flyonspeed/OnSpeed-Gen2/Hardware/Photos/IMG_1484.jpg

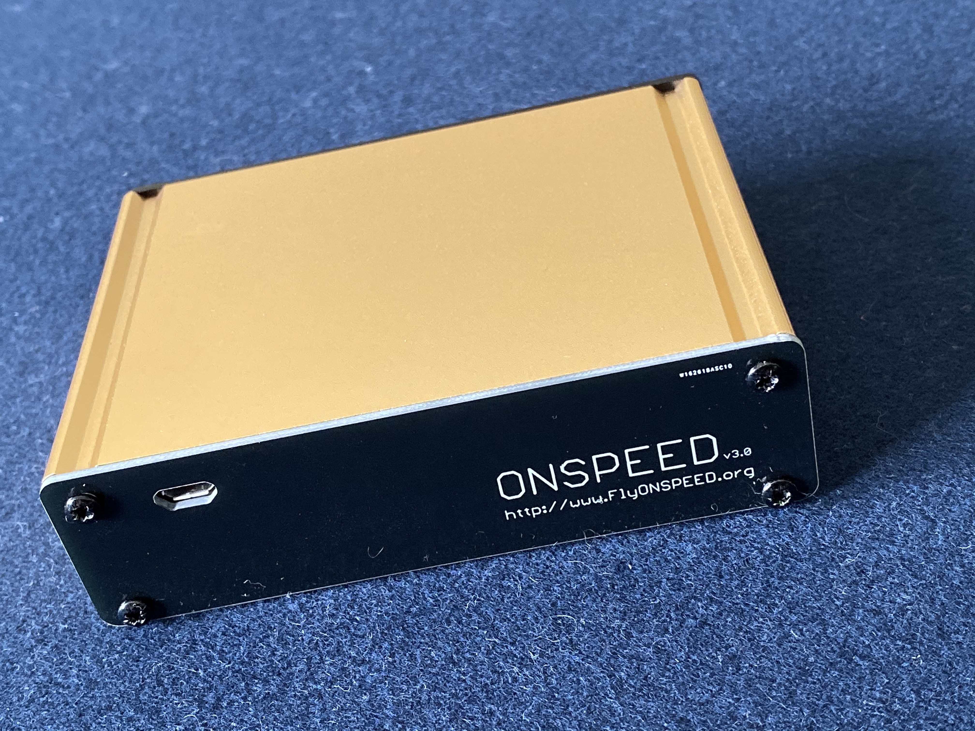
Hardware/Photos/IMG_1484.jpg
