flyonspeed/OnSpeed-Gen2/Hardware/Photos/IMG_8985.JPG

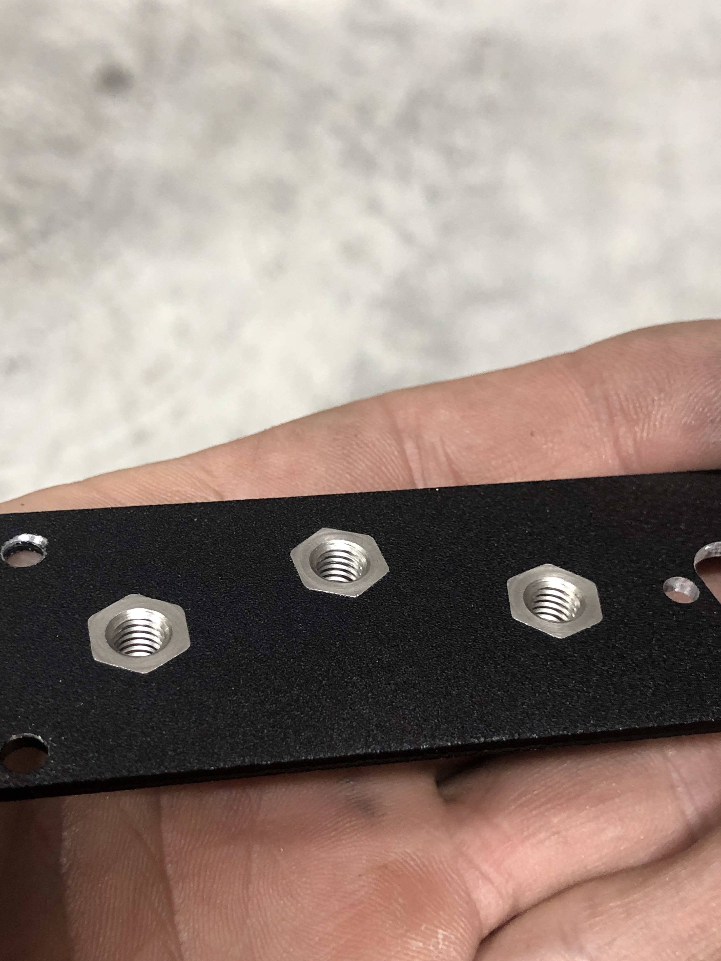
Hardware/Photos/IMG_8985.JPG
