flyonspeed/OnSpeed-Gen2/Hardware/Photos/IMG_8987.JPG

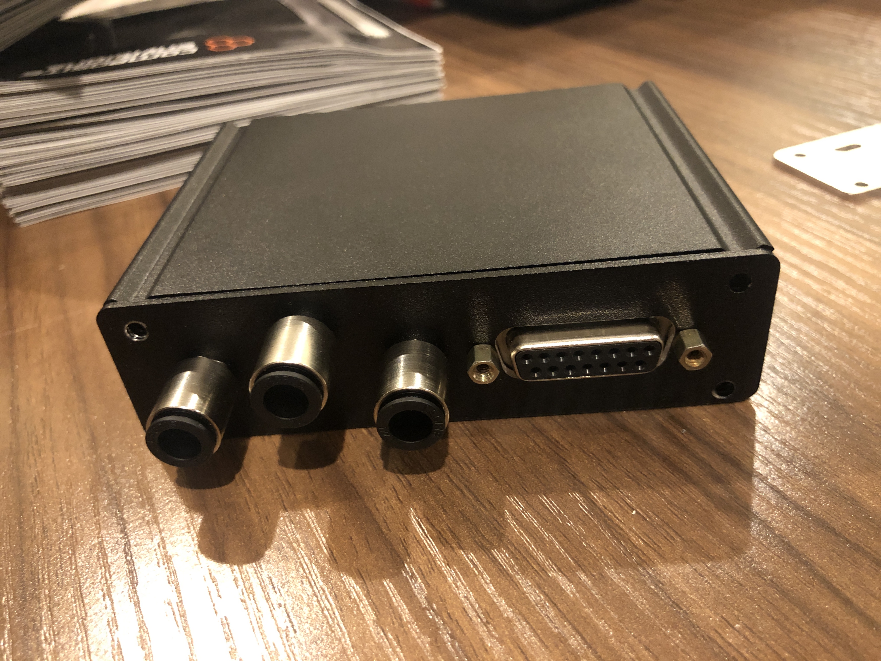
Hardware/Photos/IMG_8987.JPG
