flyonspeed/OnSpeed-Gen2/Hardware/Photos/IMG_9418.jpeg

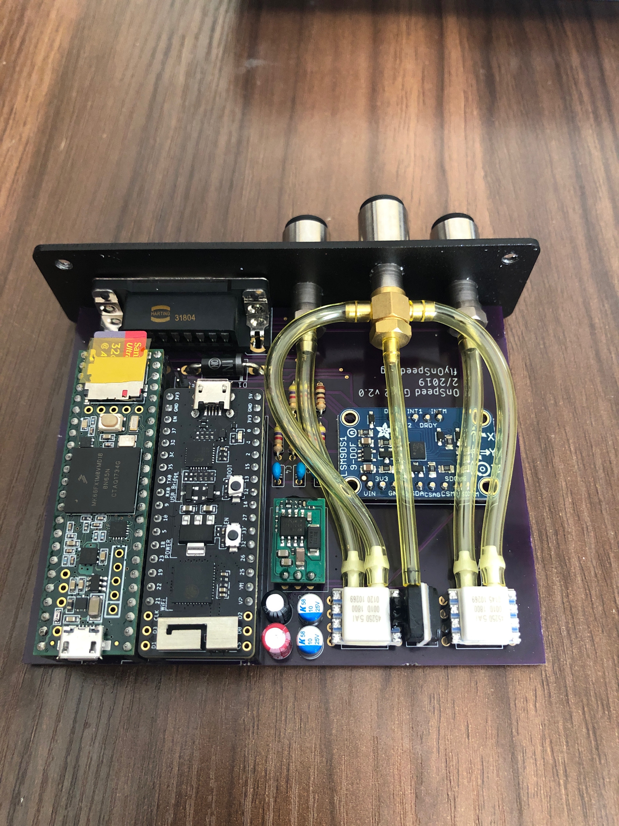
Hardware/Photos/IMG_9418.jpeg
