flyonspeed/OnSpeed-Gen2/Software/OnSpeedTeensy_AHRS/WifiSerial.ino

void readWifiSerial()
{
// read Wifi serial
// look for wifi serial command

if (Serial4.available()>0)
  {
//$LIST!
//$DELETE filename!
//$PRINT filename!
//$STOPLIVEDATA!
//$STARTLIVEDATA!
//$FORMAT!
//$NOLOAD!
//$REBOOT!
//$SENDCONFIGSTRING!
//$SAVECONFIGSTRING<configstring>!
//$VOLUME
//$FLAPS
//$AOA
//$AUDIOTEST
serialWifiCmdChar = Serial4.read();
Serial.print(serialWifiCmdChar);
if (serialWifiCmdBufferSize >=3070)
      {       
      serialWifiCmdBufferSize=0; // don't let the command buffer overflow
      }
  if (serialWifiCmdChar!='!')
    {
    if (serialWifiCmdBufferSize==0 && serialWifiCmdChar!='$')
        {
        //drop character if command doesn't start with $                
        }
         else
              {
              serialWifiCmdBuffer[serialWifiCmdBufferSize]=serialWifiCmdChar;
              serialWifiCmdBufferSize++;
              }
    }          
    if (serialWifiCmdBufferSize>0 && serialWifiCmdChar=='!')
          { 
          // process command          
            if (strstr(serialWifiCmdBuffer, "$LIST"))
              {
              // list files
              timersOff();              
              Serial.println("file list requested on Wifi");
              bool orig_sdLogging=sdLogging;
              if (orig_sdLogging) sdLogging=false; // turn off sdLogging  
              sendWifiSerialString("<filelist>\n");
              ListFile=Sd.open("/", O_READ);
              if (!ListFile) Serial.println("SD card missing or unreadable");
              while(true) {
                          checkWatchdog();
                           FsFile entry =  ListFile.openNextFile();
                           if (!entry) {
                                         // no more files                                                                      
//                                         fileList+="<eof>";
                                         sendWifiSerialString("<eof>\n");
                                         break;
                                        }                           
                           if (!entry.isDirectory())
                              {
                              // only list files in root folder, no directories
                              char entryName[15];
                              entry.getName(entryName, sizeof(entryName));
                              sendWifiSerialString(String(entryName));
                              sendWifiSerialString(":");
                              char entrySize[20];
                              sprintf(entrySize, "%" PRIu64, entry.size());
                              sendWifiSerialString(String(entrySize));
                              sendWifiSerialString("\n");                              
                              }                             
                           entry.close();
                           }                     
               
              if (orig_sdLogging) sdLogging=true; // turn sd logging back on if it was originally on.
              timersOn();
              
              } else
                     if (strstr(serialWifiCmdBuffer, "$DELETE"))
                        {
                        // delete file                        
                        memcpy(listfileFileName,serialWifiCmdBuffer+8,serialWifiCmdBufferSize-7);
                        Sd.remove(listfileFileName);
                        Serial4.println();
                        Serial4.print("Deleted: ");
                        Serial4.println(listfileFileName);
                        } else
                              if (strstr(serialWifiCmdBuffer, "$PRINT"))
                                 {
                                 bool orig_sdLogging=sdLogging;
                                 if (orig_sdLogging)
                                      {
                                      sdLogging=false; // turn off sdLogging                                            
                                      Serial.println("STOPPED SD logging during file transfer.");
                                      }
                                 timersOff();                                                                                                   
                                 // print file contents
                                 Serial.println(serialWifiCmdBuffer);
                                 memcpy(listfileFileName,serialWifiCmdBuffer+7,serialWifiCmdBufferSize-6);                                 
                                 checkWatchdog();
                                 delay(1000);
                                 byte sendBuffer[1460];
                                 int totalBytes=0;
                                 ListFile=Sd.open(listfileFileName, O_READ);
                                 if (ListFile) {     
                                              // read from the file until the end
                                              bool packetFailed=false;
                                              while (ListFile.available())
                                              {      
                                                     checkWatchdog();                                                                                                                                                                                                                                                                                                               
                                                     // wait for serial packet to leave
                                                     if (!packetFailed) totalBytes=ListFile.read(sendBuffer,1459);
                                                     //Serial.println(totalBytes);
                                                     byte checksum=0;                                                     
                                                     for (int i=0;i<totalBytes;i++)
                                                         {                                                     
                                                         while(Serial4.availableForWrite()==0) {};                                                                                                                                                 
                                                         Serial4.write(sendBuffer[i]);                                                                                          
                                                         checksum+=sendBuffer[i];
                                                         }
                                                     Serial4.write(checksum);
                                                     filesendtimer=millis();
                                                     filesendtimeout=false;
                                                     //Serial.println("waiting for checksum");
                                                     while(true)
                                                                      {
                                                                      checkWatchdog();
                                                                      // check for timeout
                                                                      if (millis()-filesendtimer > 5000)
                                                                        {
                                                                         filesendtimeout=true;                                                                         
                                                                         break;  
                                                                        }
                                                                                                                                          
                                                                      // wait for ACK
                                                                      if (Serial4.available())
                                                                        {                                                                                                                                                   
                                                                          byte receivedChecksum=Serial4.read();
                                                                          if (receivedChecksum!=checksum)
                                                                              {
                                                                              packetFailed=true;
                                                                              Serial.print("bad checksum - ");
                                                                              Serial.print(totalBytes);
                                                                              Serial.print(" / ");
                                                                              Serial.print(checksum,HEX);
                                                                              Serial.print(":");
                                                                              Serial.println(receivedChecksum,HEX);
                                                                              Serial.println("resending...");
                                                                              } else
                                                                                    {
                                                                                    packetFailed=false;
                                                                                    }
                                                                         break; // break out of ACK hold                                                                                                                                                                                                                       
                                                                        }                                                                        
                                                                      
                                                                      } // while
                                                         if (filesendtimeout) 
                                                                    {
                                                                      Serial.println("file transfer timeout");
                                                                      break;                                                                                  
                                                                    }                                                               
                                                         // }
                                              }
                                              // close the file:                                              
                                              ListFile.close();                                              
                                              
                                              
                                            } else {
                                              // if the file didn't open, print an error
                                              Serial.print("Could not open file: ");
                                              Serial.println(listfileFileName);
                                              Serial4.print("<404>");
                                              
                                            }                                
                                 if (orig_sdLogging)
                                    {
                                    sdLogging=true; // turn sd logging back on if it was originally on.                                                                        
                                    Serial.println("STARTED SD logging.");
                                    }
                                 timersOn();
                                 } else
                                         
                                         if (strstr(serialWifiCmdBuffer, "$STOPLIVEDATA"))
                                         {
                                         //LiveDisplayTimer.end(); // stop display data 
                                         sendWifiData=false;                                        
                                         Serial.println("STOPPED Live Data. (Wifi Request)");
                                         } else
                                              if (strstr(serialWifiCmdBuffer, "$STARTLIVEDATA"))
                                                 {                                                 
                                                 sendWifiData=true;
                                                 Serial.println("STARTED Live Data. (Wifi Request)");
                                                 } else

                                                   if (strstr(serialWifiCmdBuffer, "$FORMAT"))
                                                          {
                                                          // delete all files                        
                                                          Serial.println("Wifi requested SD format");
                                                           bool orig_sdLogging=sdLogging;
                                                           if (orig_sdLogging) sdLogging=false; // turn off sdLogging 


                                                            ExFatFormatter exFatFormatter;
                                                            FatFormatter fatFormatter;                                                            
                                                            m_card = cardFactory.newCard(SdioConfig(FIFO_SDIO));
                                                            if ((!m_card || m_card->errorCode())) {
                                                                 Serial.print("FORMAT ERROR: Cannot initialize SD card. ");
                                                                 Serial.println(m_card->errorCode());
                                                                 Serial4.println("<formaterror></formaterror>");                                                                 
                                                              } else                                                               
                                                                 {
                                                                  cardSectorCount = m_card->sectorCount();
                                                                  // erase card first
                                                                    Serial.println("Erasing card");
                                                                    uint32_t const ERASE_SIZE = 262144L;
                                                                    uint32_t firstBlock = 0;
                                                                    uint32_t lastBlock;
                                                                    do {
                                                                        lastBlock = firstBlock + ERASE_SIZE - 1;
                                                                        if (lastBlock >= cardSectorCount)
                                                                            {
                                                                            lastBlock = cardSectorCount - 1;
                                                                            }
                                                                        if (!m_card->erase(firstBlock, lastBlock))
                                                                            {
                                                                            Serial.println("Card erase failed");
                                                                            }
                                                                       firstBlock += ERASE_SIZE;
                                                                       checkWatchdog();
                                                                       } while (firstBlock < cardSectorCount);

                                                                  
                                                                    // Format exFAT if larger than 32GB.
                                                                    bool rtn = cardSectorCount > 67108864 ?
                                                                      exFatFormatter.format(m_card, sectorBuffer, &Serial) :
                                                                      fatFormatter.format(m_card, sectorBuffer, &Serial);                                                                  
                                                                    if (!rtn) {
                                                                      Serial.println("FORMAT ERROR: Could not format SD Card.");
                                                                      Serial4.println("<FORMATERROR>Could not format SD Card</FORMATERROR>");
                                                                    } else
                                                                          {
                                                                          Serial.print("SD card format completed. Card size: ");
                                                                          Serial.print(cardSectorCount*5.12e-7);
                                                                          Serial.println("GBytes");
                                                                          Serial4.printf("<FORMATDONE>%.1f GB</FORMATDONE>\n",cardSectorCount*5.12e-7);
                                                                          delay(300);
                                                                          // initialize card, 
                                                                         byte sdBeginTries=0;
                                                                         sdAvailable=Sd.begin(SdioConfig(FIFO_SDIO));
                                                                         while (!sdAvailable && sdBeginTries<5)
                                                                               {
                                                                               //try up to 5 times
                                                                               Serial.println("Reintializing SD card.");
                                                                               sdAvailable=Sd.begin(SdioConfig(FIFO_SDIO));
                                                                               delay(200);
                                                                               sdBeginTries++;
                                                                               }
                                                                          //sdAvailable=Sd.begin(SdioConfig(FIFO_SDIO));
                                                                          if (!sdAvailable) Serial.println("SD card couldn't be initialized");
                                                                          configString="";
                                                                          configurationToString(configString);
                                                                          saveConfigurationToFile(configFilename,configString);
                                                                          configString="";
                                                                          // card is empty create new log file
                                                                          createLogFile();
                                                                                                                                                                                                                           
                                                                          }                                                                    
                                                                 }  
                                                                                                                    
                                                          if (orig_sdLogging)
                                                                {
                                                                sdLogging=true; // turn sd logging back on if it was originally on.
                                                                }
                                                          } else
                                                              if (strstr(serialWifiCmdBuffer, "$PFWDBIAS"))
                                                                  {                                                                  
                                                                  SensorTimer.end(); // stop polling the sensors on the timer so we can poll them here
                                                                  Serial.println("Wifi: Getting Pfwd bias...");
                                                                  // get Pfwd bias
                                                                  long PfwdTotal=0;                                                                
                                                                  for (int i=1;i<=500;i++)
                                                                      {
                                                                      PfwdTotal+=GetPressurePfwd();
                                                                      checkWatchdog();
                                                                      delay(2);
                                                                      }
                                                                 Serial4.printf("<PFWDBIAS>%i</PFWDBIAS>",round(PfwdTotal/500));
                                                                 SensorTimer.begin(SensorRead,SENSOR_INTERVAL);                                                                                                                               
                                                                  } else
                                                                      if (strstr(serialWifiCmdBuffer, "$P45BIAS"))
                                                                      {                                                                  
                                                                      SensorTimer.end(); // stop polling the sensors on the timer so we can poll them here
                                                                      Serial.println("Wifi: Getting P45 bias...");
                                                                      // get Pfwd bias                                                                      
                                                                      long P45Total=0;
                                                                      for (int i=1;i<=500;i++)
                                                                          {                                                                          
                                                                          P45Total+=GetPressureP45();
                                                                          delay(2);
                                                                          checkWatchdog();
                                                                          }
                                                                      Serial4.printf("<P45BIAS>%i</P45BIAS>",round(P45Total/500));
                                                                      SensorTimer.begin(SensorRead,SENSOR_INTERVAL);                                                                                                                               
                                                                      } else
                                                                            if (strstr(serialWifiCmdBuffer, "$FLAPS"))
                                                                                {                                                                                                                                              
                                                                                Serial.println("Wifi: Getting Flap position");
                                                                                int flapPotTotal=0;
                                                                                for (int i=0;i<100;i++)
                                                                                    {
                                                                                    flapPotTotal+=analogRead(FLAP_PIN);
                                                                                    checkWatchdog();
                                                                                    delay(10);
                                                                                    }                                                                                                      
                                                                                Serial4.printf("<FLAPS>%i</FLAPS>",round(flapPotTotal/100));                                                                                                                                
                                                                                } else
                                                                                  if (strstr(serialWifiCmdBuffer, "$VOLUME"))
                                                                                        {                                                                                                                                              
                                                                                        Serial.println("Wifi: Getting Volume position");
                                                                                        int volumePotTotal=0;
                                                                                        for (int i=0;i<100;i++)
                                                                                            {
                                                                                            volumePotTotal+=analogRead(VOLUME_PIN);
                                                                                            checkWatchdog();
                                                                                            delay(10);
                                                                                            }                                                                                                              
                                                                                        Serial4.printf("<VOLUME>%i</VOLUME>",round(volumePotTotal/100));                                                                                                                                
                                                                                        } else                                                                                                          
                                                                                              if (strstr(serialWifiCmdBuffer, "$AUDIOTEST"))                                                                                                                                                                          
                                                                                                {
                                                                                                Serial.println("Wifi: Testing audio");
                                                                                                timersOff();
                                                                                                Serial.println("Wifi: Playing Left audio test");                                                                                                                  
                                                                                                 ampLeft.gain(1);
                                                                                                 ampRight.gain(0);
                                                                                                 voice1.play(AudioSampleOnspeed_left_speaker);
                                                                                                checkWatchdog();
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
                                                                                                                                          for (unsigned int i=0;i<configContent.length();i++) calcCRC+=configContent[i];
                                                                                                                                          if (String(calcCRC,HEX)==checksumString)
                                                                                                                                              {
                                                                                                                                              // checksum ok.
                                                                                                                                              configString="<CONFIG>"+configContent+"</CONFIG>"; // strip checksum tag when saving config
                                                                                                                                              if (loadConfigFromString(configString))
                                                                                                                                                  {                                                                                                                                                
                                                                                                                                                  saveConfigurationToFile(configFilename,configString);
                                                                                                                                                  setVolume(volumePercent);
                                                                                                                                                  configureAxes();
                                                                                                                                                  Serial4.print("<CONFIGSAVED></CONFIGSAVED>"); 
                                                                                                                                                  Serial.println("Wifi: Loaded new configuration");                                                                                                                
                                                                                                                                                  } else Serial4.print("<CONFIGERROR>Could not load configuration</CONFIGERROR>");                                                                                                                                              
                                                                                                                                          
                                                                                                                                                } else
                                                                                                                                                      {
                                                                                                                                                      //checksum failed
                                                                                                                                                      Serial4.print("<CONFIGERROR>Transmission Error. Checksum failed. Try again.</CONFIGERROR>");
                                                                                                                                                      Serial.println("CONFIG checksum failed");
                                                                                                                                                      }
                                                                                                                                           checkWatchdog();
                                                                                                                                          // clean up after the strings 
                                                                                                                                          configString="";
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
                                                                                                                                                            timersOn(); 
                                                                                                                                                            sdLogging=true;    
                                                                                                                                                            } else
                                                                                                                                                                if (strstr(serialWifiCmdBuffer, "$SENSORCONFIG"))
                                                                                                                                                                    {
                                                                                                                                                                    // sensor bias configuration
                                                                                                                                                                     float aircraftPitch=stringToFloat(getConfigValue(serialWifiCmdBuffer,"AIRCRAFTPITCH"));
                                                                                                                                                                     float aircraftRoll=stringToFloat(getConfigValue(serialWifiCmdBuffer,"AIRCRAFTROLL"));
                                                                                                                                                                     float aircraftPAlt=stringToFloat(getConfigValue(serialWifiCmdBuffer,"AIRCRAFTPALT"));
                                                                                                                                                                     sdLogging=false;
                                                                                                                                                                     timersOff();

                                                                                                                                                                     Serial.println("Wifi: SensorConfig request");
                                                                                                                                                                     // sample sensors
                                                                                                                                                                     long P45Total=0;
                                                                                                                                                                     long PFwdTotal=0;
                                                                                                                                                                     long PStaticTotal=0;
                                                                                                                                                                     float aVertTotal=0.00;
                                                                                                                                                                     float aLatTotal=0.00;
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
                                                                                                                                                                          }
                                                                                                                                                                       
                                                                                                                                                                     // calculate pitch from averaged accelerometer reading
                                                                                                                                                                     float calcPitch=atan2((aFwdTotal/sensorReadCount), sqrt((aLatTotal/sensorReadCount)* (aLatTotal/sensorReadCount) + (aVertTotal/sensorReadCount) *(aVertTotal/sensorReadCount))) * 57.2957;
                                                                                                                                                                     float calcRoll =-atan2((aLatTotal/sensorReadCount), sqrt((aFwdTotal/sensorReadCount)* (aFwdTotal/sensorReadCount) + (aVertTotal/sensorReadCount) *(aVertTotal/sensorReadCount))) * 57.2957;                                                                                                                                                                     
                                                                                                                                                                     // adjust pitch bias (aircraft pitch -calcPitch)
                                                                                                                                                                     pitchBias=aircraftPitch-calcPitch;
                                                                                                                                                                     rollBias=aircraftRoll-calcRoll;
                                                                                                                                                                     Serial.printf("aircraftPitch: %.2f,aircraftRoll: %.2f,calcPitch: %.2f,calcRoll: %.2f",aircraftPitch,aircraftRoll,calcPitch,calcRoll);
                                                                                                                                                                     pFwdBias= int((PFwdTotal/sensorReadCount));
                                                                                                                                                                     p45Bias= int((P45Total/sensorReadCount));
                                                                                                                                                                     float PStatic= float((PStaticTotal/sensorReadCount));
                                                                                                                                                                     float aircraftPressure=29.92125535*pow(((288-0.0065*0.3048*aircraftPAlt)/288),5.2561)*33.8639; // https://www.weather.gov/media/epz/wxcalc/stationPressure.pdf from inHg to milliBars.
                                                                                                                                                                     pStaticBias=aircraftPressure - PStatic;

                                                                                                                                                                     
                                                                                                                                                                     gxBias=-gxTotal/sensorReadCount;
                                                                                                                                                                     gyBias=-gyTotal/sensorReadCount;
                                                                                                                                                                     gzBias=-gzTotal/sensorReadCount;
                                                                                                                                                                     
 
                                                                                                                                                                     String resultString="PfwdBias: "+ String(pFwdBias)+"<br>";
                                                                                                                                                                     resultString+=" P45Bias: "+ String(p45Bias)+"<br>";
                                                                                                                                                                     resultString+=" gxBias: "+ floatToString(gxBias)+"<br>";
                                                                                                                                                                     resultString+=" gyBias: "+ floatToString(gyBias)+"<br>";
                                                                                                                                                                     resultString+=" gzBias: "+ floatToString(gzBias)+"<br>";
                                                                                                                                                                     resultString+=" measured Pitch: "+ String(calcPitch)+"<br>"; 
                                                                                                                                                                     resultString+=" pitchBias: "+ String(pitchBias)+"<br>";
                                                                                                                                                                     resultString+=" measured Roll: "+ String(calcRoll)+"<br>"; 
                                                                                                                                                                     resultString+=" rollBias: "+ String(rollBias)+"<br>"; 
                                                                                                                                                                     resultString+=" staticBias: "+ String(pStaticBias)+"<br>";                                                                                                                                                                     
                                                                                                                                                                     configString="";
                                                                                                                                                                     configurationToString(configString);
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
                                                                                                                                                                                            }
                                                                                                                                                                                             
                                                                                                                                                                                        // calculate pitch from averaged accelerometer reading                                                                                                                                                                                       
                                                                                                                                                                                        float calcPitchAngle=calcPitch(aFwdTotal/sensorReadCount, aLatTotal/sensorReadCount, aVertTotal/sensorReadCount);
                                                                                                                                                                                        float calcRollAngle=calcRoll(aFwdTotal/sensorReadCount, aLatTotal/sensorReadCount, aVertTotal/sensorReadCount);
                                                                                                                                                                                        float PStatic= float((PStaticTotal/sensorReadCount));
                                                                                                                                                                                        Palt=145366.45*(1-pow((PStatic+pStaticBias)/1013.25,0.190284)); //Pstatic in milliBars,Palt in feet
                                                                                                                                                                                        Serial4.printf("<RESPONSE><PITCH>%.2f</PITCH><ROLL>%.2f</ROLL><PALT>%.2f</PALT></RESPONSE>",calcPitchAngle,-calcRollAngle,Palt);                                                                                                                                                                                     
                                                                                                                                                                                        timersOn();
                                                                                                                                                                                        sdLogging=true;
                                                                                                                                                                                        }  else
                                                                                                                                                                                              if (strstr(serialWifiCmdBuffer, "$VERSION"))
                                                                                                                                                                                                        {
                                                                                                                                                                                                         Serial.println("Wifi: Version request");
                                                                                                                                                                                                         sendWifiSerialString("<VERSION>"+String(VERSION)+"</VERSION>");                                                                                                                                                                                                    
                                                                                                                                                                                                        }
                                                                                                                                                                                                         else                                                                                                                                                                                                                                                                                                        
                                                                                                                                                                                                             if (strstr(serialWifiCmdBuffer, "$VNOCHIMETEST"))                                                                                                                                                                          
                                                                                                                                                                                                                    {
                                                                                                                                                                                                                    Serial.println("Wifi: VNO chime audiotest");
                                                                                                                                                                                                                    timersOff();                                                                                                                                                                                                         
                                                                                                                                                                                                                    voice1.play(AudioSampleVnochime);
                                                                                                                                                                                                                    checkWatchdog();
                                                                                                                                                                                                                    delay (2500);
                                                                                                                                                                                                                    checkWatchdog();                                                                                                                                                                                                       
                                                                                                                                                                                                                    timersOn();
                                                                                                                                                                                                                    Serial.println("Wifi: VNOCHIMETEST Complete");
                                                                                                                                                                                                                    Serial4.println("<VNOCHIMETEST>Done.</VNOCHIMETEST>");
                                                                                                                                                                                                                    }

          // reset cmdBuffer
          memset(serialWifiCmdBuffer,0,sizeof(serialWifiCmdBuffer));
          serialWifiCmdBufferSize=0;
          }  
  } // if serial.available wifi

}

void sendWifiSerialString(String serialString)
{
  for (unsigned int i=0; i<serialString.length();i++)
  {
  Serial4.flush();
  while(Serial4.availableForWrite() == 0)
    {
    checkWatchdog();
    };
  Serial4.print(serialString[i]);  
  checkWatchdog();
  }
}
