flyonspeed/OnSpeed-Gen2/Software/OnSpeedWifi/html_liveview.h

const char htmlLiveView[] PROGMEM = R"=====(
<style>

html, body { margin:0; padding: 0 5px; overflow:hidden;min-height:100% }

#container {width:100%}  

svg {position:absolute;margin:0 auto; display: block;}

#datafields {position:relative; margin-top:5px;font-family: "Arial, Helvetica, sans-serif";font-size:16px; left:0px;}

#footer {display: block;;position:fixed; bottom:2px; width: 100%;font-family: "Arial, Helvetica, sans-serif";font-size:14px;}

#footer-warning {text-align: center;margin-left: -10px; width: 100%;font-family: "Arial, Helvetica, sans-serif";font-size:12px;background-color:white}

#status {display:flex;justify-content: space-between;padding-bottom:10px;}

#switch {margin-right: 20px;}  

#status-label {align-self: flex-end;}  

/*! XS */

@media (orientation: portrait) {

  svg {  margin: 0 auto 0 0px; }

}

@media (orientation: landscape) {

 /* svg { height: 60vh;}*/  

}

</style>

<script language="javascript" type="text/javascript">
 var wsUri = "ws://192.168.0.1:81";
 var lastUpdate= Date.now();
 var lastDisplay=Date.now(); 
 var AOA=0;
 var IAS=0;
 var PAlt=0;
 var GLoad=1;
 var GLoadLat=0;
 var PitchAngle=0;
 var RollAngle=0;
 var smoothingAlpha=.9;
 var liveConnecting=false;
 var flightPath=0;
 var iVSI=0;
 var derivedAOA=0;
 var pitchRate=0;

 var calSource="";
setInterval(updateAge,500); 
var websocket;


function init()

  {            
     writeToStatus("CONNECTING...");
     liveConnecting=true;
     setTimeout(connectWebSocket, 300);   
    
  }



function connectWebSocket()

  { 

    websocket = new WebSocket(wsUri);

    websocket.onopen = function(evt) { onOpen(evt) };

    websocket.onclose = function(evt) { onClose(evt) };

    websocket.onmessage = function(evt) { onMessage(evt) };

    websocket.onerror = function(evt) { onError(evt) };

  }



  function onOpen(evt)

  {
    writeToStatus("CONNECTED");
  }



  function onClose(evt)
  {
    writeToStatus("Reconnecting...");    
    if (!liveConnecting) setTimeout(connectWebSocket, 10);
  }

  

 function map(x, in_min, in_max, out_min, out_max)

{

if ((in_max - in_min) + out_min ==0) return 0;

  return (x - in_min) * (out_max - out_min) / (in_max - in_min) + out_min;

}  



  function onMessage(evt)

  {    
   // reply to prevent timeouts
   liveConnecting=false;
   // connected, got data
   // smoother values are display with the formula: value = measurement*alpha + previous value*(1-alpha)   

   try {

   //console.log(evt.data);

   OnSpeedArray = evt.data.split(",");

   var OnSpeed = new Object();

   OnSpeed.AOA= OnSpeedArray[1]; 

   OnSpeed.Pitch= OnSpeedArray[2]; 

   OnSpeed.Roll= OnSpeedArray[3]; 

   OnSpeed.IAS= OnSpeedArray[4]; 

   OnSpeed.PAlt= OnSpeedArray[5]; 

   OnSpeed.verticalGLoad= OnSpeedArray[6]; 

   OnSpeed.lateralGLoad= OnSpeedArray[7]; 

   OnSpeed.alphaVA= OnSpeedArray[8]; 

   OnSpeed.LDmax= OnSpeedArray[9]; 

   OnSpeed.OnspeedFast= OnSpeedArray[10]; 

   OnSpeed.OnspeedSlow= OnSpeedArray[11]; 

   OnSpeed.OnspeedWarn= OnSpeedArray[12]; 

   OnSpeed.flapsPos= OnSpeedArray[13]; 

   OnSpeed.coeffP= OnSpeedArray[14];

   OnSpeed.dataMark= OnSpeedArray[15];

   OnSpeed.kalmanVSI=OnSpeedArray[16];
   
   OnSpeed.flightPath=OnSpeedArray[17]

   OnSpeed.PitchRate= OnSpeedArray[18];
   
   OnSpeed.DecelRate= OnSpeedArray[19];

   OnSpeed.calSourceID= OnSpeedArray[20];
      
   OnSpeed.CRC= OnSpeedArray[21]; 

   var crc_string=OnSpeed.AOA+','+OnSpeed.Pitch+','+OnSpeed.Roll+','+OnSpeed.IAS+','+OnSpeed.PAlt+','+OnSpeed.verticalGLoad+','+OnSpeed.lateralGLoad+','+OnSpeed.alphaVA+','+OnSpeed.LDmax+','+OnSpeed.OnspeedFast+','+OnSpeed.OnspeedSlow+','+OnSpeed.OnspeedWarn+','+OnSpeed.flapsPos+','+OnSpeed.coeffP+','+OnSpeed.dataMark+','+OnSpeed.kalmanVSI+','+OnSpeed.flightPath+','+OnSpeed.PitchRate+','+OnSpeed.DecelRate+','+OnSpeed.calSourceID;
   //console.log("CRC",crc_string);

   var crc_calc=0;

   for (i=0;i<crc_string.length;i++)

       {

       crc_calc+=crc_string.charCodeAt(i);

     crc_calc=crc_calc & 0xFF;

     }

    if (OnSpeed.CRC==crc_calc)

    {

    // CRC ok, use values

    AOA=(OnSpeed.AOA*smoothingAlpha+AOA*(1-smoothingAlpha)).toFixed(2);

    IAS=(OnSpeed.IAS*smoothingAlpha+IAS*(1-smoothingAlpha)).toFixed(2);

    PAlt=(OnSpeed.PAlt*smoothingAlpha+PAlt*(1-smoothingAlpha)).toFixed(2);

    GLoad=(OnSpeed.verticalGLoad*smoothingAlpha+GLoad*(1-smoothingAlpha)).toFixed(2);

    GLoadLat=(OnSpeed.lateralGLoad*smoothingAlpha+GLoadLat*(1-smoothingAlpha)).toFixed(2);

    PitchAngle=(OnSpeed.Pitch*smoothingAlpha+PitchAngle*(1-smoothingAlpha)).toFixed(2);

    RollAngle=(OnSpeed.Roll*smoothingAlpha+RollAngle*(1-smoothingAlpha)).toFixed(2);

    iVSI=(OnSpeed.kalmanVSI*smoothingAlpha+iVSI*(1-smoothingAlpha)).toFixed(2);

    flightPath=(OnSpeed.flightPath*smoothingAlpha+flightPath*(1-smoothingAlpha)).toFixed(2);

    derivedAOA=(PitchAngle-flightPath).toFixed(2);

    pitchRate=parseFloat(OnSpeed.PitchRate);

    LDmax=parseFloat(OnSpeed.LDmax);

    OnspeedFast=parseFloat(OnSpeed.OnspeedFast);

    OnspeedSlow=parseFloat(OnSpeed.OnspeedSlow);

    OnspeedWarn=parseFloat(OnSpeed.OnspeedWarn);
    lastUpdate=Date.now();
    // 0= IMU, 1=VN-300, 2=AFS/SkyView, 3=Dynon D10, 4=G5, 5=G3X, 6=MGL
      switch (parseInt(OnSpeed.calSourceID)) {
      case 0:
      calSource="Internal IMU";
      break;
      case 1: calSource="VectorNav VN-200/300";
        break;
      case 2: calSource="SkyView/Advanced";
        break;
      case 3: calSource="Dynon D10/D100";
        break;
      case 4: calSource="Garmin G5";
        break;
      case 5: calSource="Garmin G3X";
        break;
      case 6: calSource="MGL iEFIS";
        break;      
      default:
        calSource='N/A';
  }
    
      writeToCalibrationSource(calSource); 

    //console.log('log:',AOA,IAS,PAlt,GLoad,GLoadLat,PitchAngle,OnSpeed.LDmax,OnSpeed.OnspeedFast,OnSpeed.OnspeedSlow,OnSpeed.OnspeedWarn);

    // move AOA line on display    

   if (AOA<=LDmax)
  
     {

     var aoaline_y=map(AOA, 0, LDmax, 278, 228);     

     } else

     if (AOA>LDmax && AOA<=OnspeedFast)

       {

       aoaline_y=map(AOA, LDmax, OnspeedFast, 228, 178);

       } else

       if (AOA>OnspeedFast && AOA<=OnspeedSlow)

         {

         aoaline_y=map(AOA, OnspeedFast, OnspeedSlow, 178, 113);

         } else

             if (AOA>OnspeedSlow)

               {

               aoaline_y=map(AOA, OnspeedSlow,OnspeedWarn, 113, 15);

               //console.log('aoaline',aoaline_y,AOA,OnspeedSlow,OnspeedWarn);

               }



    document.getElementById("aoaline").setAttribute("y", aoaline_y);

// calc ldmax dot locations

 ldmax_y=228+3;

 document.getElementById("ldmaxleft").setAttribute("cy", ldmax_y);

 document.getElementById("ldmaxright").setAttribute("cy", ldmax_y);

// show onspeed dot

// update attitude

updateAttitude(OnSpeed.Pitch,OnSpeed.Roll);

 if (AOA>OnspeedFast && AOA<=OnspeedSlow) document.getElementById("onspeeddot").style.visibility="visible"; else document.getElementById("onspeeddot").style.visibility="hidden"; 

   

}  else console.log('CRC error'); 

    

   } catch (e) {

           console.log('JSON parsing error:'+e.name+': '+e.message);

           }         

   

   if (Date.now()-lastDisplay>=500)

       {

       if (AOA > -20) document.getElementById("aoa").innerHTML=AOA; else document.getElementById("aoa").innerHTML='N/A';

       document.getElementById("ias").innerHTML=IAS +' kts';

       document.getElementById("palt").innerHTML=PAlt+' ft';

       document.getElementById("ivsi").innerHTML=iVSI+' fpm';

       document.getElementById("gload").innerHTML=GLoad+' G';

       document.getElementById("gloadLat").innerHTML=GLoadLat+' G';

       document.getElementById("pitch").innerHTML=PitchAngle+'&#176;';

       document.getElementById("roll").innerHTML=RollAngle+'&#176;';

       document.getElementById("flightpath").innerHTML=flightPath+'&#176;';

       document.getElementById("derivedaoa").innerHTML=derivedAOA+'&#176;';

       document.getElementById("datamark").innerHTML=OnSpeed.dataMark;

       document.getElementById("flapspos").innerHTML=OnSpeed.flapsPos+'&#176;';

       lastDisplay=Date.now(); 

   }

  

  }



 function onError(evt)

  {
    console.log(evt.data);
    
    writeToStatus(evt.data);

  }  



  function updateAge()

  {

  var age=((Date.now()-lastUpdate)/1000).toFixed(1);   

  if (document.getElementById("age"))

    {

   document.getElementById("age").innerHTML=age +' sec';

   if (age>=1)  document.getElementById("age").style="color:red"; else document.getElementById("age").style="color:black";         

   if ((age>=3) && !liveConnecting) init();    

   }

  }



 function writeToStatus(message)

  {

    var status = document.getElementById("connectionstatus");

    status.innerHTML = message;

  } 

 function writeToCalibrationSource(calSource)
  {

    var status = document.getElementById("calibrationsource");

    status.innerHTML = calSource;

  }   

 function updateAttitude(pitch,roll) {

  if (document.getElementById("attitude")==null || document.getElementById("attitude").style.visibility!="visible") return; //don't update attitude if attitude indicator is not visible

    roll=roll*-1;

    var p = (pitch * 2.50);

    var t = 'translate(50,50) rotate(' + roll + ') translate(0,' + p + ')' ;

    var id_roll = document.querySelector('#onspeed-attitude-pos');

    if (id_roll!=null) id_roll.setAttribute('transform',t);

  var id_dial = document.querySelector('#onspeed-attitude-dial');

  x = 50;

    y = 50;

    var t =  'translate(' + x + ',' + y + ')' + 'rotate(' + roll + ')';

    id_dial.setAttribute('transform',t);   

  }



function toggleAOA(state)

  {

  //console.log(state);

  if (state)

      {

      document.getElementById("aoaindexer").style.visibility="visible";

      document.getElementById("attitude").style.visibility="hidden";   

      } else

            {

            document.getElementById("aoaindexer").style.visibility="hidden";

            document.getElementById("attitude").style.visibility="visible";   

            }

}            

updateAttitude(0,0);

//window.addEventListener("load", function() {init();}, false);  

</script>

<div id="container">

  <div id="aoaindexer">

  <svg version="1.1" viewBox="0 0 210 297" width="100%" style="height: 70vh">

 <g>

  <circle cx="98.171" cy="787.76" r="133.84" fill="#07a33f" stroke-width="1.8089"/>

  <rect transform="rotate(-15.029)" x="50.364" y="33.747" width="15.615" height="89.228" fill="#cc3837"/>

  <rect transform="matrix(-.9658 -.2593 -.2593 .9658 0 0)" x="-148.06" y="-19.129" width="15.615" height="89.228" fill="#cc3837"/>

  <rect transform="matrix(.9658 .2593 .2593 -.9658 0 0)" x="127.53" y="-255.15" width="15.615" height="89.228" fill="#f49421"/>

  <rect transform="rotate(164.97)" x="-70.153" y="-307.83" width="15.615" height="89.228" fill="#f49421"/>

  <path d="m101.8 113.26c-17.123 0-31.526 12.231-34.92 28.385 5.203-2.6e-4 10.398 1.6e-4 15.598 0 2.9178-7.8426 10.401-13.371 19.323-13.371 8.922 0 16.413 5.5289 19.336 13.371 5.198 1.6e-4 10.403-2.8e-4 15.602 0-3.397-16.154-17.815-28.385-34.938-28.385zm-35.121 41.774c2.9176 16.746 17.577 29.609 35.121 29.609 17.544 0 32.218-12.863 35.138-29.609-5.1216-2.8e-4 -10.25 1.6e-4 -15.371 0-2.5708 8.4824-10.391 14.574-19.767 14.574-9.3764 0-17.183-6.0913-19.75-14.574-5.1246 1.4e-4 -10.244-2.8e-4 -15.371 0z" color="#000000" color-rendering="auto" dominant-baseline="auto" fill="#07a33f" image-rendering="auto" shape-rendering="auto" solid-color="#000000" style="font-feature-settings:normal;font-variant-alternates:normal;font-variant-caps:normal;font-variant-ligatures:normal;font-variant-numeric:normal;font-variant-position:normal;isolation:auto;mix-blend-mode:normal;paint-order:markers fill stroke;shape-padding:0;text-decoration-color:#000000;text-decoration-line:none;text-decoration-style:solid;text-indent:0;text-orientation:mixed;text-transform:none;white-space:normal"/>

  <circle id="onspeeddot" cx="101.8" cy="148.91" r="18" fill="#07a33f" stroke-width=".81089" visibility="hidden"/>

 </g>

 <g fill="#241f1c">

  <rect id="aoaline" x="52.187" y="144.91" width="100" height="6.6921" style="paint-order:markers fill stroke"/>

  <circle id="ldmaxleft" cx="46.801" cy="228" r="3.346" stroke-width="1.0419"/>

  <circle id="ldmaxright" cx="157.53" cy="228" r="3.346" stroke-width="1.0419"/>

 </g>

</svg>

</div>

<div id="attitude" style="visibility:hidden;">

  <svg id="onspeed-attitude" xmlns="http://www.w3.org/2000/svg" width="100%" height="300px" viewBox="0 0 100 100">

    <g id="onspeed-attitude-pos" stroke-width="0.5" stroke="#fff" fill="#fff\

       transform="translate(50,50) rotate(0)\

       text-anchor='middle' font-family="sans-serif" font-size="6">

  

      <rect fill="#29B6F6" stroke-width="0" x="-100" y="-200" width="200" height="200"></rect>

      <rect fill="#8B4513" stroke-width="0" x="-100" y="0"  width="200" height="200"></rect>

  

      <!-- pitch up -->

      <line x1="-8"  y1="-6.25"   x2="8"  y2="-6.25"/>

      <line x1="-16" y1="-12"     x2="-4" y2="-12"  />

      <text stroke-width="0.1" x="0" y="-10">5</text>

      <line x1="4"   y1="-12"     x2="16" y2="-12"  />

  

      <line x1="-8"  y1="-18.75"  x2="8"  y2="-18.75"/>

      <line x1="-16" y1="-25"     x2="-4" y2="-25"  />

      <text stroke-width="0.1" x="0" y="-23">10</text>

      <line x1="4"   y1="-25"     x2="16" y2="-25"  />

  

      <line x1="-8"  y1="-31.25"   x2="8"  y2="-31.25"/>

      <line x1="-16" y1="-37.5"    x2="-4" y2="-37.5"  />

      <text stroke-width="0.1" x="0" y="-35">15</text>

      <line x1="4"   y1="-37.5"    x2="16" y2="-37.5"  />

  

      <line x1="-8"  y1="-43.75"   x2="8"  y2="-43.75"/>

      <line x1="-16" y1="-50.0"    x2="-4" y2="-50.0"  />

      <text stroke-width="0.1" x="0" y="-48">20</text>

      <line x1="4"   y1="-50.0"    x2="16" y2="-50.0"  />

  

      <line x1="-8"  y1="-56.25"   x2="8"  y2="-56.25"/>

      <line x1="-16" y1="-62.5"    x2="-4" y2="-62.5"  />

      <text stroke-width="0.1" x="0" y="-60.5">25</text>

      <line x1="4"   y1="-62.5"    x2="16" y2="-62.5"  />

  

      <line x1="-8"  y1="-68.75"   x2="8"  y2="-68.75"/>

      <line x1="-16" y1="-75.0"    x2="-4" y2="-75.0" />

      <text stroke-width="0.1" x="0" y="-73">30</text>

      <line x1="4"   y1="-75.0"    x2="16" y2="-75.0" />

  

      <!-- pitch down -->

      <line x1="-8"  y1="6.25"   x2="8"  y2="6.25"/>

      <line x1="-16" y1="12"     x2="-4" y2="12"  />

      <text stroke-width="0.1" x="0" y="14">5</text>

      <line x1="4"   y1="12"     x2="16" y2="12"  />

  

      <line x1="-8"  y1="18.75"   x2="8"  y2="18.75"/>

      <line x1="-16" y1="25"     x2="-4" y2="25"  />

      <text stroke-width="0.1" x="0" y="27">10</text>

      <line x1="4"   y1="25"     x2="16" y2="25"  />

  

      <line x1="-8"  y1="31.25"   x2="8"  y2="31.25"/>

      <line x1="-16" y1="37.5"    x2="-4" y2="37.5"  />

      <text stroke-width="0.1" x="0" y="39">15</text>

      <line x1="4"   y1="37.5"    x2="16" y2="37.5"  />

  

      <line x1="-8"  y1="43.75"   x2="8"  y2="43.75"/>

      <line x1="-16" y1="50.0"    x2="-4" y2="50.0"  />

      <text stroke-width="0.1" x="0" y="52">20</text>

      <line x1="4"   y1="50.0"    x2="16" y2="50.0"  />

  

      <line x1="-8"  y1="56.25"   x2="8"  y2="56.25"/>

      <line x1="-16" y1="62.5"    x2="-4" y2="62.5"  />

      <text stroke-width="0.1" x="0" y="64.5">25</text>

      <line x1="4"   y1="62.5"    x2="16" y2="62.5"  />

  

      <line x1="-8"  y1="68.75"   x2="8"  y2="68.75"/>

      <line x1="-16" y1="75.0"    x2="-4" y2="75.0" />

      <text stroke-width="0.1" x="0" y="77">30</text>

      <line x1="4"   y1="75.0"    x2="16" y2="75.0" />

  

    </g>

    <g stroke-width="2" stroke="#ff0">

    <line x1="30" y1="50" x2="43" y2="50"></line>

    <line x1="42" y1="50" x2="42" y2="53"></line>

  

    <line  x1="49" y1="50" x2="51" y2="50"/>

  

    <line x1="58" y1="53" x2="58" y2="50"></line>

    <line x1="57" y1="50" x2="70" y2="50"></line>

    </g>  

  <g id='onspeed-attitude-dial' stroke-width="1" transform="translate(50,49) rotate(0)" stroke="#fff">

      <line stroke-width='1.5' x1='20.00' y1='-34.64' x2='24.50' y2='-42.44' />

      <line stroke-width='1.5' x1='34.64' y1='-20.00' x2='42.44' y2='-24.50' />

      <line stroke-width='1.5' x1='40.00' y1='0.00' x2='49.00' y2='0.00' />

      <line stroke-width='1.5' x1='-20.00' y1='-34.64' x2='-24.50' y2='-42.44' />

      <line stroke-width='1.5' x1='-34.64' y1='-20.00' x2='-42.44' y2='-24.50' />

      <line stroke-width='1.5' x1='-40.00' y1='-0.00' x2='-49.00' y2='-0.00' />

      <line x1='6.95' y1='-39.39' x2='7.81' y2='-44.32' />

      <line x1='13.68' y1='-37.59' x2='15.39' y2='-42.29' />

      <line x1='28.28' y1='-28.28' x2='31.82' y2='-31.82' />

      <line x1='-6.95' y1='-39.39' x2='-7.81' y2='-44.32' />

      <line x1='-13.68' y1='-37.59' x2='-15.39' y2='-42.29' />

      <line x1='-28.28' y1='-28.28' x2='-31.82' y2='-31.82' />

      <line x1='0.00' y1='-40.00' x2='0.00' y2='-45.00' />

  

      <path fill="#fff" d="M-4 -50 L4 -50 L 0 -40 z"></path>

    </g>  

  

    <g stroke-width="1" stroke="#ff0" fill="#ff0">

      <path d="M46 18 L54 18 L50 11 z"></path>

    </g>



  </svg>

  

  </div>



  <div id="datafields"></span>

    AOA: <span id="aoa"></span> <br>
  
    Derived AOA: <span id="derivedaoa"></span> <br>

    FlightPath: <span id="flightpath"></span> <br>
    
    IAS: <span id="ias"></span> <br>

    Press. Alt: <span id="palt"></span> <br>

    iVSI: <span id="ivsi"></span> <br>

    Vert G: <span id="gload"></span> <br>

    Lat G: <span id="gloadLat"></span> <br>

    Pitch: <span id="pitch"></span> <br>

    Roll: <span id="roll"></span> <br>    

    DataMark: <span id="datamark"></span> <br>

    Flaps: <span id="flapspos"></span> <br>

    Age: <span id="age"></span> <br>

  </div>

  <div id="footer">

    <div id="status">

     <div id="status-label">

       <strong>Status:</strong> <span id="connectionstatus">DISCONNECTED.</span><br>
       <strong>Calibration Source:</strong> <span id="calibrationsource">N/A</span>

     </div>

     <div id="switch">

     <div class="switch-field">

     <input type="radio" id="switchAOA" name="toggleAOA"  onClick="toggleAOA(true)" value="yes" checked/>

     <label for="switchAOA">AOA</label>

     <input type="radio" id="switchAHRS" name="toggleAOA" onClick="toggleAOA(false)" value="no" />

     <label for="switchAHRS">AHRS</label>

   </div>

   </div>

   </div>

   

   <div id="footer-warning">  

   For diagnostic purposes only. NOT SAFE FOR FLIGHT

   </div>

  </div>

</div>

<script>init()</script>
)=====";
