flyonspeed/OnSpeed-Gen2/Software/OnSpeedWifi/javascript_chartist1.h

const char jsChartist1[] PROGMEM = R"=====(
<script language="javascript" type="text/javascript">
/* Chartist.js 0.11.4
 * Copyright © 2019 Gion Kunz
 * Free to use under either the WTFPL license or the MIT license.
 * https://raw.githubusercontent.com/gionkunz/chartist-js/master/LICENSE-WTFPL
 * https://raw.githubusercontent.com/gionkunz/chartist-js/master/LICENSE-MIT
 */

!function(a,b){"function"==typeof define&&define.amd?define("Chartist",[],function(){return a.Chartist=b()}):"object"==typeof module&&module.exports?module.exports=b():a.Chartist=b()}(this,function(){var a={version:"0.11.4"};return function(a,b){"use strict";var c=a.window,d=a.document;b.namespaces={svg:"http://www.w3.org/2000/svg",xmlns:"http://www.w3.org/2000/xmlns/",xhtml:"http://www.w3.org/1999/xhtml",xlink:"http://www.w3.org/1999/xlink",ct:"http://gionkunz.github.com/chartist-js/ct"},b.noop=function(a){return a},b.alphaNumerate=function(a){return String.fromCharCode(97+a%26)},b.extend=function(a){var c,d,e;for(a=a||{},c=1;c<arguments.length;c++){d=arguments[c];for(var f in d)e=d[f],"object"!=typeof e||null===e||e instanceof Array?a[f]=e:a[f]=b.extend(a[f],e)}return a},b.replaceAll=function(a,b,c){return a.replace(new RegExp(b,"g"),c)},b.ensureUnit=function(a,b){return"number"==typeof a&&(a+=b),a},b.quantity=function(a){if("string"==typeof a){var b=/^(\d+)\s*(.*)$/g.exec(a);return{value:+b[1],unit:b[2]||void 0}}return{value:a}},b.querySelector=function(a){return a instanceof Node?a:d.querySelector(a)},b.times=function(a){return Array.apply(null,new Array(a))},b.sum=function(a,b){return a+(b?b:0)},b.mapMultiply=function(a){return function(b){return b*a}},b.mapAdd=function(a){return function(b){return b+a}},b.serialMap=function(a,c){var d=[],e=Math.max.apply(null,a.map(function(a){return a.length}));return b.times(e).forEach(function(b,e){var f=a.map(function(a){return a[e]});d[e]=c.apply(null,f)}),d},b.roundWithPrecision=function(a,c){var d=Math.pow(10,c||b.precision);return Math.round(a*d)/d},b.precision=8,b.escapingMap={"&":"&amp;","<":"&lt;",">":"&gt;",'"':"&quot;","'":"&#039;"},b.serialize=function(a){return null===a||void 0===a?a:("number"==typeof a?a=""+a:"object"==typeof a&&(a=JSON.stringify({data:a})),Object.keys(b.escapingMap).reduce(function(a,c){return b.replaceAll(a,c,b.escapingMap[c])},a))},b.deserialize=function(a){if("string"!=typeof a)return a;a=Object.keys(b.escapingMap).reduce(function(a,c){return b.replaceAll(a,b.escapingMap[c],c)},a);try{a=JSON.parse(a),a=void 0!==a.data?a.data:a}catch(c){}return a},b.createSvg=function(a,c,d,e){var f;return c=c||"100%",d=d||"100%",Array.prototype.slice.call(a.querySelectorAll("svg")).filter(function(a){return a.getAttributeNS(b.namespaces.xmlns,"ct")}).forEach(function(b){a.removeChild(b)}),f=new b.Svg("svg").attr({width:c,height:d}).addClass(e),f._node.style.width=c,f._node.style.height=d,a.appendChild(f._node),f},b.normalizeData=function(a,c,d){var e,f={raw:a,normalized:{}};return f.normalized.series=b.getDataArray({series:a.series||[]},c,d),e=f.normalized.series.every(function(a){return a instanceof Array})?Math.max.apply(null,f.normalized.series.map(function(a){return a.length})):f.normalized.series.length,f.normalized.labels=(a.labels||[]).slice(),Array.prototype.push.apply(f.normalized.labels,b.times(Math.max(0,e-f.normalized.labels.length)).map(function(){return""})),c&&b.reverseData(f.normalized),f},b.safeHasProperty=function(a,b){return null!==a&&"object"==typeof a&&a.hasOwnProperty(b)},b.isDataHoleValue=function(a){return null===a||void 0===a||"number"==typeof a&&isNaN(a)},b.reverseData=function(a){a.labels.reverse(),a.series.reverse();for(var b=0;b<a.series.length;b++)"object"==typeof a.series[b]&&void 0!==a.series[b].data?a.series[b].data.reverse():a.series[b]instanceof Array&&a.series[b].reverse()},b.getDataArray=function(a,c,d){function e(a){if(b.safeHasProperty(a,"value"))return e(a.value);if(b.safeHasProperty(a,"data"))return e(a.data);if(a instanceof Array)return a.map(e);if(!b.isDataHoleValue(a)){if(d){var c={};return"string"==typeof d?c[d]=b.getNumberOrUndefined(a):c.y=b.getNumberOrUndefined(a),c.x=a.hasOwnProperty("x")?b.getNumberOrUndefined(a.x):c.x,c.y=a.hasOwnProperty("y")?b.getNumberOrUndefined(a.y):c.y,c}return b.getNumberOrUndefined(a)}}return a.series.map(e)},b.normalizePadding=function(a,b){return b=b||0,"number"==typeof a?{top:a,right:a,bottom:a,left:a}:{top:"number"==typeof a.top?a.top:b,right:"number"==typeof a.right?a.right:b,bottom:"number"==typeof a.bottom?a.bottom:b,left:"number"==typeof a.left?a.left:b}},b.getMetaData=function(a,b){var c=a.data?a.data[b]:a[b];return c?c.meta:void 0},b.orderOfMagnitude=function(a){return Math.floor(Math.log(Math.abs(a))/Math.LN10)},b.projectLength=function(a,b,c){return b/c.range*a},b.getAvailableHeight=function(a,c){return Math.max((b.quantity(c.height).value||a.height())-(c.chartPadding.top+c.chartPadding.bottom)-c.axisX.offset,0)},b.getHighLow=function(a,c,d){function e(a){if(void 0!==a)if(a instanceof Array)for(var b=0;b<a.length;b++)e(a[b]);else{var c=d?+a[d]:+a;g&&c>f.high&&(f.high=c),h&&c<f.low&&(f.low=c)}}c=b.extend({},c,d?c["axis"+d.toUpperCase()]:{});var f={high:void 0===c.high?-Number.MAX_VALUE:+c.high,low:void 0===c.low?Number.MAX_VALUE:+c.low},g=void 0===c.high,h=void 0===c.low;return(g||h)&&e(a),(c.referenceValue||0===c.referenceValue)&&(f.high=Math.max(c.referenceValue,f.high),f.low=Math.min(c.referenceValue,f.low)),f.high<=f.low&&(0===f.low?f.high=1:f.low<0?f.high=0:f.high>0?f.low=0:(f.high=1,f.low=0)),f},b.isNumeric=function(a){return null!==a&&isFinite(a)},b.isFalseyButZero=function(a){return!a&&0!==a},b.getNumberOrUndefined=function(a){return b.isNumeric(a)?+a:void 0},b.isMultiValue=function(a){return"object"==typeof a&&("x"in a||"y"in a)},b.getMultiValue=function(a,c){return b.isMultiValue(a)?b.getNumberOrUndefined(a[c||"y"]):b.getNumberOrUndefined(a)},b.rho=function(a){function b(a,c){return a%c===0?c:b(c,a%c)}function c(a){return a*a+1}if(1===a)return a;var d,e=2,f=2;if(a%2===0)return 2;do e=c(e)%a,f=c(c(f))%a,d=b(Math.abs(e-f),a);while(1===d);return d},b.getBounds=function(a,c,d,e){function f(a,b){return a===(a+=b)&&(a*=1+(b>0?o:-o)),a}var g,h,i,j=0,k={high:c.high,low:c.low};k.valueRange=k.high-k.low,k.oom=b.orderOfMagnitude(k.valueRange),k.step=Math.pow(10,k.oom),k.min=Math.floor(k.low/k.step)*k.step,k.max=Math.ceil(k.high/k.step)*k.step,k.range=k.max-k.min,k.numberOfSteps=Math.round(k.range/k.step);var l=b.projectLength(a,k.step,k),m=l<d,n=e?b.rho(k.range):0;if(e&&b.projectLength(a,1,k)>=d)k.step=1;else if(e&&n<k.step&&b.projectLength(a,n,k)>=d)k.step=n;else for(;;){if(m&&b.projectLength(a,k.step,k)<=d)k.step*=2;else{if(m||!(b.projectLength(a,k.step/2,k)>=d))break;if(k.step/=2,e&&k.step%1!==0){k.step*=2;break}}if(j++>1e3)throw new Error("Exceeded maximum number of iterations while optimizing scale step!")}var o=2.221e-16;for(k.step=Math.max(k.step,o),h=k.min,i=k.max;h+k.step<=k.low;)h=f(h,k.step);for(;i-k.step>=k.high;)i=f(i,-k.step);k.min=h,k.max=i,k.range=k.max-k.min;var p=[];for(g=k.min;g<=k.max;g=f(g,k.step)){var q=b.roundWithPrecision(g);q!==p[p.length-1]&&p.push(q)}return k.values=p,k},b.polarToCartesian=function(a,b,c,d){var e=(d-90)*Math.PI/180;return{x:a+c*Math.cos(e),y:b+c*Math.sin(e)}},b.createChartRect=function(a,c,d){var e=!(!c.axisX&&!c.axisY),f=e?c.axisY.offset:0,g=e?c.axisX.offset:0,h=a.width()||b.quantity(c.width).value||0,i=a.height()||b.quantity(c.height).value||0,j=b.normalizePadding(c.chartPadding,d);h=Math.max(h,f+j.left+j.right),i=Math.max(i,g+j.top+j.bottom);var k={padding:j,width:function(){return this.x2-this.x1},height:function(){return this.y1-this.y2}};return e?("start"===c.axisX.position?(k.y2=j.top+g,k.y1=Math.max(i-j.bottom,k.y2+1)):(k.y2=j.top,k.y1=Math.max(i-j.bottom-g,k.y2+1)),"start"===c.axisY.position?(k.x1=j.left+f,k.x2=Math.max(h-j.right,k.x1+1)):(k.x1=j.left,k.x2=Math.max(h-j.right-f,k.x1+1))):(k.x1=j.left,k.x2=Math.max(h-j.right,k.x1+1),k.y2=j.top,k.y1=Math.max(i-j.bottom,k.y2+1)),k},b.createGrid=function(a,c,d,e,f,g,h,i){var j={};j[d.units.pos+"1"]=a,j[d.units.pos+"2"]=a,j[d.counterUnits.pos+"1"]=e,j[d.counterUnits.pos+"2"]=e+f;var k=g.elem("line",j,h.join(" "));i.emit("draw",b.extend({type:"grid",axis:d,index:c,group:g,element:k},j))},b.createGridBackground=function(a,b,c,d){var e=a.elem("rect",{x:b.x1,y:b.y2,width:b.width(),height:b.height()},c,!0);d.emit("draw",{type:"gridBackground",group:a,element:e})},b.createLabel=function(a,c,e,f,g,h,i,j,k,l,m){var n,o={};if(o[g.units.pos]=a+i[g.units.pos],o[g.counterUnits.pos]=i[g.counterUnits.pos],o[g.units.len]=c,o[g.counterUnits.len]=Math.max(0,h-10),l){var p=d.createElement("span");p.className=k.join(" "),p.setAttribute("xmlns",b.namespaces.xhtml),p.innerText=f[e],p.style[g.units.len]=Math.round(o[g.units.len])+"px",p.style[g.counterUnits.len]=Math.round(o[g.counterUnits.len])+"px",n=j.foreignObject(p,b.extend({style:"overflow: visible;"},o))}else n=j.elem("text",o,k.join(" ")).text(f[e]);m.emit("draw",b.extend({type:"label",axis:g,index:e,group:j,element:n,text:f[e]},o))},b.getSeriesOption=function(a,b,c){if(a.name&&b.series&&b.series[a.name]){var d=b.series[a.name];return d.hasOwnProperty(c)?d[c]:b[c]}return b[c]},b.optionsProvider=function(a,d,e){function f(a){var f=h;if(h=b.extend({},j),d)for(i=0;i<d.length;i++){var g=c.matchMedia(d[i][0]);g.matches&&(h=b.extend(h,d[i][1]))}e&&a&&e.emit("optionsChanged",{previousOptions:f,currentOptions:h})}function g(){k.forEach(function(a){a.removeListener(f)})}var h,i,j=b.extend({},a),k=[];if(!c.matchMedia)throw"window.matchMedia not found! Make sure you're using a polyfill.";if(d)for(i=0;i<d.length;i++){var l=c.matchMedia(d[i][0]);l.addListener(f),k.push(l)}return f(),{removeMediaQueryListeners:g,getCurrentOptions:function(){return b.extend({},h)}}},b.splitIntoSegments=function(a,c,d){var e={increasingX:!1,fillHoles:!1};d=b.extend({},e,d);for(var f=[],g=!0,h=0;h<a.length;h+=2)void 0===b.getMultiValue(c[h/2].value)?d.fillHoles||(g=!0):(d.increasingX&&h>=2&&a[h]<=a[h-2]&&(g=!0),g&&(f.push({pathCoordinates:[],valueData:[]}),g=!1),f[f.length-1].pathCoordinates.push(a[h],a[h+1]),f[f.length-1].valueData.push(c[h/2]));return f}}(this||global,a),function(a,b){"use strict";b.Interpolation={},b.Interpolation.none=function(a){var c={fillHoles:!1};return a=b.extend({},c,a),function(c,d){for(var e=new b.Svg.Path,f=!0,g=0;g<c.length;g+=2){var h=c[g],i=c[g+1],j=d[g/2];void 0!==b.getMultiValue(j.value)?(f?e.move(h,i,!1,j):e.line(h,i,!1,j),f=!1):a.fillHoles||(f=!0)}return e}},b.Interpolation.simple=function(a){var c={divisor:2,fillHoles:!1};a=b.extend({},c,a);var d=1/Math.max(1,a.divisor);return function(c,e){for(var f,g,h,i=new b.Svg.Path,j=0;j<c.length;j+=2){var k=c[j],l=c[j+1],m=(k-f)*d,n=e[j/2];void 0!==n.value?(void 0===h?i.move(k,l,!1,n):i.curve(f+m,g,k-m,l,k,l,!1,n),f=k,g=l,h=n):a.fillHoles||(f=k=h=void 0)}return i}},b.Interpolation.cardinal=function(a){var c={tension:1,fillHoles:!1};a=b.extend({},c,a);var d=Math.min(1,Math.max(0,a.tension)),e=1-d;return function f(c,g){var h=b.splitIntoSegments(c,g,{fillHoles:a.fillHoles});if(h.length){if(h.length>1){var i=[];return h.forEach(function(a){i.push(f(a.pathCoordinates,a.valueData))}),b.Svg.Path.join(i)}if(c=h[0].pathCoordinates,g=h[0].valueData,c.length<=4)return b.Interpolation.none()(c,g);for(var j,k=(new b.Svg.Path).move(c[0],c[1],!1,g[0]),l=0,m=c.length;m-2*!j>l;l+=2){var n=[{x:+c[l-2],y:+c[l-1]},{x:+c[l],y:+c[l+1]},{x:+c[l+2],y:+c[l+3]},{x:+c[l+4],y:+c[l+5]}];j?l?m-4===l?n[3]={x:+c[0],y:+c[1]}:m-2===l&&(n[2]={x:+c[0],y:+c[1]},n[3]={x:+c[2],y:+c[3]}):n[0]={x:+c[m-2],y:+c[m-1]}:m-4===l?n[3]=n[2]:l||(n[0]={x:+c[l],y:+c[l+1]}),k.curve(d*(-n[0].x+6*n[1].x+n[2].x)/6+e*n[2].x,d*(-n[0].y+6*n[1].y+n[2].y)/6+e*n[2].y,d*(n[1].x+6*n[2].x-n[3].x)/6+e*n[2].x,d*(n[1].y+6*n[2].y-n[3].y)/6+e*n[2].y,n[2].x,n[2].y,!1,g[(l+2)/2])}return k}return b.Interpolation.none()([])}},b.Interpolation.monotoneCubic=function(a){var c={fillHoles:!1};return a=b.extend({},c,a),function d(c,e){var f=b.splitIntoSegments(c,e,{fillHoles:a.fillHoles,increasingX:!0});if(f.length){if(f.length>1){var g=[];return f.forEach(function(a){g.push(d(a.pathCoordinates,a.valueData))}),b.Svg.Path.join(g)}if(c=f[0].pathCoordinates,e=f[0].valueData,c.length<=4)return b.Interpolation.none()(c,e);var h,i,j=[],k=[],l=c.length/2,m=[],n=[],o=[],p=[];for(h=0;h<l;h++)j[h]=c[2*h],k[h]=c[2*h+1];for(h=0;h<l-1;h++)o[h]=k[h+1]-k[h],p[h]=j[h+1]-j[h],n[h]=o[h]/p[h];for(m[0]=n[0],m[l-1]=n[l-2],h=1;h<l-1;h++)0===n[h]||0===n[h-1]||n[h-1]>0!=n[h]>0?m[h]=0:(m[h]=3*(p[h-1]+p[h])/((2*p[h]+p[h-1])/n[h-1]+(p[h]+2*p[h-1])/n[h]),isFinite(m[h])||(m[h]=0));for(i=(new b.Svg.Path).move(j[0],k[0],!1,e[0]),h=0;h<l-1;h++)i.curve(j[h]+p[h]/3,k[h]+m[h]*p[h]/3,j[h+1]-p[h]/3,k[h+1]-m[h+1]*p[h]/3,j[h+1],k[h+1],!1,e[h+1]);return i}return b.Interpolation.none()([])}},b.Interpolation.step=function(a){var c={postpone:!0,fillHoles:!1};return a=b.extend({},c,a),function(c,d){for(var e,f,g,h=new b.Svg.Path,i=0;i<c.length;i+=2){var j=c[i],k=c[i+1],l=d[i/2];void 0!==l.value?(void 0===g?h.move(j,k,!1,l):(a.postpone?h.line(j,f,!1,g):h.line(e,k,!1,l),h.line(j,k,!1,l)),e=j,f=k,g=l):a.fillHoles||(e=f=g=void 0)}return h}}}(this||global,a),function(a,b){"use strict";b.EventEmitter=function(){function a(a,b){d[a]=d[a]||[],d[a].push(b)}function b(a,b){d[a]&&(b?(d[a].splice(d[a].indexOf(b),1),0===d[a].length&&delete d[a]):delete d[a])}function c(a,b){d[a]&&d[a].forEach(function(a){a(b)}),d["*"]&&d["*"].forEach(function(c){c(a,b)})}var d=[];return{addEventHandler:a,removeEventHandler:b,emit:c}}}(this||global,a),function(a,b){"use strict";function c(a){var b=[];if(a.length)for(var c=0;c<a.length;c++)b.push(a[c]);return b}function d(a,c){var d=c||this.prototype||b.Class,e=Object.create(d);b.Class.cloneDefinitions(e,a);var f=function(){var a,c=e.constructor||function(){};return a=this===b?Object.create(e):this,c.apply(a,Array.prototype.slice.call(arguments,0)),a};return f.prototype=e,f["super"]=d,f.extend=this.extend,f}function e(){var a=c(arguments),b=a[0];return a.splice(1,a.length-1).forEach(function(a){Object.getOwnPropertyNames(a).forEach(function(c){delete b[c],Object.defineProperty(b,c,Object.getOwnPropertyDescriptor(a,c))})}),b}b.Class={extend:d,cloneDefinitions:e}}(this||global,a),function(a,b){"use strict";function c(a,c,d){return a&&(this.data=a||{},this.data.labels=this.data.labels||[],this.data.series=this.data.series||[],this.eventEmitter.emit("data",{type:"update",data:this.data})),c&&(this.options=b.extend({},d?this.options:this.defaultOptions,c),this.initializeTimeoutId||(this.optionsProvider.removeMediaQueryListeners(),this.optionsProvider=b.optionsProvider(this.options,this.responsiveOptions,this.eventEmitter))),this.initializeTimeoutId||this.createChart(this.optionsProvider.getCurrentOptions()),this}function d(){return this.initializeTimeoutId?i.clearTimeout(this.initializeTimeoutId):(i.removeEventListener("resize",this.resizeListener),this.optionsProvider.removeMediaQueryListeners()),this}function e(a,b){return this.eventEmitter.addEventHandler(a,b),this}function f(a,b){return this.eventEmitter.removeEventHandler(a,b),this}function g(){i.addEventListener("resize",this.resizeListener),this.optionsProvider=b.optionsProvider(this.options,this.responsiveOptions,this.eventEmitter),this.eventEmitter.addEventHandler("optionsChanged",function(){this.update()}.bind(this)),this.options.plugins&&this.options.plugins.forEach(function(a){a instanceof Array?a[0](this,a[1]):a(this)}.bind(this)),this.eventEmitter.emit("data",{type:"initial",data:this.data}),this.createChart(this.optionsProvider.getCurrentOptions()),this.initializeTimeoutId=void 0}function h(a,c,d,e,f){this.container=b.querySelector(a),this.data=c||{},this.data.labels=this.data.labels||[],this.data.series=this.data.series||[],this.defaultOptions=d,this.options=e,this.responsiveOptions=f,this.eventEmitter=b.EventEmitter(),this.supportsForeignObject=b.Svg.isSupported("Extensibility"),this.supportsAnimations=b.Svg.isSupported("AnimationEventsAttribute"),this.resizeListener=function(){this.update()}.bind(this),this.container&&(this.container.__chartist__&&this.container.__chartist__.detach(),this.container.__chartist__=this),this.initializeTimeoutId=setTimeout(g.bind(this),0)}var i=a.window;b.Base=b.Class.extend({constructor:h,optionsProvider:void 0,container:void 0,svg:void 0,eventEmitter:void 0,createChart:function(){throw new Error("Base chart type can't be instantiated!")},update:c,detach:d,on:e,off:f,version:b.version,supportsForeignObject:!1})}(this||global,a),function(a,b){"use strict";function c(a,c,d,e,f){a instanceof Element?this._node=a:(this._node=y.createElementNS(b.namespaces.svg,a),"svg"===a&&this.attr({"xmlns:ct":b.namespaces.ct})),c&&this.attr(c),d&&this.addClass(d),e&&(f&&e._node.firstChild?e._node.insertBefore(this._node,e._node.firstChild):e._node.appendChild(this._node))}function d(a,c){return"string"==typeof a?c?this._node.getAttributeNS(c,a):this._node.getAttribute(a):(Object.keys(a).forEach(function(c){if(void 0!==a[c])if(c.indexOf(":")!==-1){var d=c.split(":");this._node.setAttributeNS(b.namespaces[d[0]],c,a[c])}else this._node.setAttribute(c,a[c])}.bind(this)),this)}function e(a,c,d,e){return new b.Svg(a,c,d,this,e)}function f(){return this._node.parentNode instanceof SVGElement?new b.Svg(this._node.parentNode):null}function g(){for(var a=this._node;"svg"!==a.nodeName;)a=a.parentNode;return new b.Svg(a)}function h(a){var c=this._node.querySelector(a);return c?new b.Svg(c):null}function i(a){var c=this._node.querySelectorAll(a);return c.length?new b.Svg.List(c):null}function j(){return this._node}function k(a,c,d,e){if("string"==typeof a){var f=y.createElement("div");f.innerHTML=a,a=f.firstChild}a.setAttribute("xmlns",b.namespaces.xmlns);var g=this.elem("foreignObject",c,d,e);return g._node.appendChild(a),g}function l(a){return this._node.appendChild(y.createTextNode(a)),this}function m(){for(;this._node.firstChild;)this._node.removeChild(this._node.firstChild);return this}function n(){return this._node.parentNode.removeChild(this._node),this.parent()}function o(a){return this._node.parentNode.replaceChild(a._node,this._node),a}function p(a,b){return b&&this._node.firstChild?this._node.insertBefore(a._node,this._node.firstChild):this._node.appendChild(a._node),this}function q(){return this._node.getAttribute("class")?this._node.getAttribute("class").trim().split(/\s+/):[]}function r(a){return this._node.setAttribute("class",this.classes(this._node).concat(a.trim().split(/\s+/)).filter(function(a,b,c){return c.indexOf(a)===b}).join(" ")),this}function s(a){var b=a.trim().split(/\s+/);return this._node.setAttribute("class",this.classes(this._node).filter(function(a){return b.indexOf(a)===-1}).join(" ")),this}function t(){return this._node.setAttribute("class",""),this}function u(){return this._node.getBoundingClientRect().height}function v(){return this._node.getBoundingClientRect().width}
)=====";
