flyonspeed/OnSpeed-Gen2/Software/OnSpeedWifi/javascript_chartist2.h

const char jsChartist2[] PROGMEM = R"=====(
function w(a,c,d){return void 0===c&&(c=!0),Object.keys(a).forEach(function(e){function f(a,c){var f,g,h,i={};a.easing&&(h=a.easing instanceof Array?a.easing:b.Svg.Easing[a.easing],delete a.easing),a.begin=b.ensureUnit(a.begin,"ms"),a.dur=b.ensureUnit(a.dur,"ms"),h&&(a.calcMode="spline",a.keySplines=h.join(" "),a.keyTimes="0;1"),c&&(a.fill="freeze",i[e]=a.from,this.attr(i),g=b.quantity(a.begin||0).value,a.begin="indefinite"),f=this.elem("animate",b.extend({attributeName:e},a)),c&&setTimeout(function(){try{f._node.beginElement()}catch(b){i[e]=a.to,this.attr(i),f.remove()}}.bind(this),g),d&&f._node.addEventListener("beginEvent",function(){d.emit("animationBegin",{element:this,animate:f._node,params:a})}.bind(this)),f._node.addEventListener("endEvent",function(){d&&d.emit("animationEnd",{element:this,animate:f._node,params:a}),c&&(i[e]=a.to,this.attr(i),f.remove())}.bind(this))}a[e]instanceof Array?a[e].forEach(function(a){f.bind(this)(a,!1)}.bind(this)):f.bind(this)(a[e],c)}.bind(this)),this}function x(a){var c=this;this.svgElements=[];for(var d=0;d<a.length;d++)this.svgElements.push(new b.Svg(a[d]));Object.keys(b.Svg.prototype).filter(function(a){return["constructor","parent","querySelector","querySelectorAll","replace","append","classes","height","width"].indexOf(a)===-1}).forEach(function(a){c[a]=function(){var d=Array.prototype.slice.call(arguments,0);return c.svgElements.forEach(function(c){b.Svg.prototype[a].apply(c,d)}),c}})}var y=a.document;b.Svg=b.Class.extend({constructor:c,attr:d,elem:e,parent:f,root:g,querySelector:h,querySelectorAll:i,getNode:j,foreignObject:k,text:l,empty:m,remove:n,replace:o,append:p,classes:q,addClass:r,removeClass:s,removeAllClasses:t,height:u,width:v,animate:w}),b.Svg.isSupported=function(a){return y.implementation.hasFeature("http://www.w3.org/TR/SVG11/feature#"+a,"1.1")};var z={easeInSine:[.47,0,.745,.715],easeOutSine:[.39,.575,.565,1],easeInOutSine:[.445,.05,.55,.95],easeInQuad:[.55,.085,.68,.53],easeOutQuad:[.25,.46,.45,.94],easeInOutQuad:[.455,.03,.515,.955],easeInCubic:[.55,.055,.675,.19],easeOutCubic:[.215,.61,.355,1],easeInOutCubic:[.645,.045,.355,1],easeInQuart:[.895,.03,.685,.22],easeOutQuart:[.165,.84,.44,1],easeInOutQuart:[.77,0,.175,1],easeInQuint:[.755,.05,.855,.06],easeOutQuint:[.23,1,.32,1],easeInOutQuint:[.86,0,.07,1],easeInExpo:[.95,.05,.795,.035],easeOutExpo:[.19,1,.22,1],easeInOutExpo:[1,0,0,1],easeInCirc:[.6,.04,.98,.335],easeOutCirc:[.075,.82,.165,1],easeInOutCirc:[.785,.135,.15,.86],easeInBack:[.6,-.28,.735,.045],easeOutBack:[.175,.885,.32,1.275],easeInOutBack:[.68,-.55,.265,1.55]};b.Svg.Easing=z,b.Svg.List=b.Class.extend({constructor:x})}(this||global,a),function(a,b){"use strict";function c(a,c,d,e,f,g){var h=b.extend({command:f?a.toLowerCase():a.toUpperCase()},c,g?{data:g}:{});d.splice(e,0,h)}function d(a,b){a.forEach(function(c,d){t[c.command.toLowerCase()].forEach(function(e,f){b(c,e,d,f,a)})})}function e(a,c){this.pathElements=[],this.pos=0,this.close=a,this.options=b.extend({},u,c)}function f(a){return void 0!==a?(this.pos=Math.max(0,Math.min(this.pathElements.length,a)),this):this.pos}function g(a){return this.pathElements.splice(this.pos,a),this}function h(a,b,d,e){return c("M",{x:+a,y:+b},this.pathElements,this.pos++,d,e),this}function i(a,b,d,e){return c("L",{x:+a,y:+b},this.pathElements,this.pos++,d,e),this}function j(a,b,d,e,f,g,h,i){return c("C",{x1:+a,y1:+b,x2:+d,y2:+e,x:+f,y:+g},this.pathElements,this.pos++,h,i),this}function k(a,b,d,e,f,g,h,i,j){return c("A",{rx:+a,ry:+b,xAr:+d,lAf:+e,sf:+f,x:+g,y:+h},this.pathElements,this.pos++,i,j),this}function l(a){var c=a.replace(/([A-Za-z])([0-9])/g,"$1 $2").replace(/([0-9])([A-Za-z])/g,"$1 $2").split(/[\s,]+/).reduce(function(a,b){return b.match(/[A-Za-z]/)&&a.push([]),a[a.length-1].push(b),a},[]);"Z"===c[c.length-1][0].toUpperCase()&&c.pop();var d=c.map(function(a){var c=a.shift(),d=t[c.toLowerCase()];return b.extend({command:c},d.reduce(function(b,c,d){return b[c]=+a[d],b},{}))}),e=[this.pos,0];return Array.prototype.push.apply(e,d),Array.prototype.splice.apply(this.pathElements,e),this.pos+=d.length,this}function m(){var a=Math.pow(10,this.options.accuracy);return this.pathElements.reduce(function(b,c){var d=t[c.command.toLowerCase()].map(function(b){return this.options.accuracy?Math.round(c[b]*a)/a:c[b]}.bind(this));return b+c.command+d.join(",")}.bind(this),"")+(this.close?"Z":"")}function n(a,b){return d(this.pathElements,function(c,d){c[d]*="x"===d[0]?a:b}),this}function o(a,b){return d(this.pathElements,function(c,d){c[d]+="x"===d[0]?a:b}),this}function p(a){return d(this.pathElements,function(b,c,d,e,f){var g=a(b,c,d,e,f);(g||0===g)&&(b[c]=g)}),this}function q(a){var c=new b.Svg.Path(a||this.close);return c.pos=this.pos,c.pathElements=this.pathElements.slice().map(function(a){return b.extend({},a)}),c.options=b.extend({},this.options),c}function r(a){var c=[new b.Svg.Path];return this.pathElements.forEach(function(d){d.command===a.toUpperCase()&&0!==c[c.length-1].pathElements.length&&c.push(new b.Svg.Path),c[c.length-1].pathElements.push(d)}),c}function s(a,c,d){for(var e=new b.Svg.Path(c,d),f=0;f<a.length;f++)for(var g=a[f],h=0;h<g.pathElements.length;h++)e.pathElements.push(g.pathElements[h]);return e}var t={m:["x","y"],l:["x","y"],c:["x1","y1","x2","y2","x","y"],a:["rx","ry","xAr","lAf","sf","x","y"]},u={accuracy:3};b.Svg.Path=b.Class.extend({constructor:e,position:f,remove:g,move:h,line:i,curve:j,arc:k,scale:n,translate:o,transform:p,parse:l,stringify:m,clone:q,splitByCommand:r}),b.Svg.Path.elementDescriptions=t,b.Svg.Path.join=s}(this||global,a),function(a,b){"use strict";function c(a,b,c,d){this.units=a,this.counterUnits=a===e.x?e.y:e.x,this.chartRect=b,this.axisLength=b[a.rectEnd]-b[a.rectStart],this.gridOffset=b[a.rectOffset],this.ticks=c,this.options=d}function d(a,c,d,e,f){var g=e["axis"+this.units.pos.toUpperCase()],h=this.ticks.map(this.projectValue.bind(this)),i=this.ticks.map(g.labelInterpolationFnc);h.forEach(function(j,k){var l,m={x:0,y:0};l=h[k+1]?h[k+1]-j:Math.max(this.axisLength-j,30),b.isFalseyButZero(i[k])&&""!==i[k]||("x"===this.units.pos?(j=this.chartRect.x1+j,m.x=e.axisX.labelOffset.x,"start"===e.axisX.position?m.y=this.chartRect.padding.top+e.axisX.labelOffset.y+(d?5:20):m.y=this.chartRect.y1+e.axisX.labelOffset.y+(d?5:20)):(j=this.chartRect.y1-j,m.y=e.axisY.labelOffset.y-(d?l:0),"start"===e.axisY.position?m.x=d?this.chartRect.padding.left+e.axisY.labelOffset.x:this.chartRect.x1-10:m.x=this.chartRect.x2+e.axisY.labelOffset.x+10),g.showGrid&&b.createGrid(j,k,this,this.gridOffset,this.chartRect[this.counterUnits.len](),a,[e.classNames.grid,e.classNames[this.units.dir]],f),g.showLabel&&b.createLabel(j,l,k,i,this,g.offset,m,c,[e.classNames.label,e.classNames[this.units.dir],"start"===g.position?e.classNames[g.position]:e.classNames.end],d,f))}.bind(this))}var e=(a.window,a.document,{x:{pos:"x",len:"width",dir:"horizontal",rectStart:"x1",rectEnd:"x2",rectOffset:"y2"},y:{pos:"y",len:"height",dir:"vertical",rectStart:"y2",rectEnd:"y1",rectOffset:"x1"}});b.Axis=b.Class.extend({constructor:c,createGridAndLabels:d,projectValue:function(a,b,c){throw new Error("Base axis can't be instantiated!")}}),b.Axis.units=e}(this||global,a),function(a,b){"use strict";function c(a,c,d,e){var f=e.highLow||b.getHighLow(c,e,a.pos);this.bounds=b.getBounds(d[a.rectEnd]-d[a.rectStart],f,e.scaleMinSpace||20,e.onlyInteger),this.range={min:this.bounds.min,max:this.bounds.max},b.AutoScaleAxis["super"].constructor.call(this,a,d,this.bounds.values,e)}function d(a){return this.axisLength*(+b.getMultiValue(a,this.units.pos)-this.bounds.min)/this.bounds.range}a.window,a.document;b.AutoScaleAxis=b.Axis.extend({constructor:c,projectValue:d})}(this||global,a),function(a,b){"use strict";function c(a,c,d,e){var f=e.highLow||b.getHighLow(c,e,a.pos);this.divisor=e.divisor||1,this.ticks=e.ticks||b.times(this.divisor).map(function(a,b){return f.low+(f.high-f.low)/this.divisor*b}.bind(this)),this.ticks.sort(function(a,b){return a-b}),this.range={min:f.low,max:f.high},b.FixedScaleAxis["super"].constructor.call(this,a,d,this.ticks,e),this.stepLength=this.axisLength/this.divisor}function d(a){return this.axisLength*(+b.getMultiValue(a,this.units.pos)-this.range.min)/(this.range.max-this.range.min)}a.window,a.document;b.FixedScaleAxis=b.Axis.extend({constructor:c,projectValue:d})}(this||global,a),function(a,b){"use strict";function c(a,c,d,e){b.StepAxis["super"].constructor.call(this,a,d,e.ticks,e);var f=Math.max(1,e.ticks.length-(e.stretch?1:0));this.stepLength=this.axisLength/f}function d(a,b){return this.stepLength*b}a.window,a.document;b.StepAxis=b.Axis.extend({constructor:c,projectValue:d})}(this||global,a),function(a,b){"use strict";function c(a){var c=b.normalizeData(this.data,a.reverseData,!0);this.svg=b.createSvg(this.container,a.width,a.height,a.classNames.chart);var d,f,g=this.svg.elem("g").addClass(a.classNames.gridGroup),h=this.svg.elem("g"),i=this.svg.elem("g").addClass(a.classNames.labelGroup),j=b.createChartRect(this.svg,a,e.padding);d=void 0===a.axisX.type?new b.StepAxis(b.Axis.units.x,c.normalized.series,j,b.extend({},a.axisX,{ticks:c.normalized.labels,stretch:a.fullWidth})):a.axisX.type.call(b,b.Axis.units.x,c.normalized.series,j,a.axisX),f=void 0===a.axisY.type?new b.AutoScaleAxis(b.Axis.units.y,c.normalized.series,j,b.extend({},a.axisY,{high:b.isNumeric(a.high)?a.high:a.axisY.high,low:b.isNumeric(a.low)?a.low:a.axisY.low})):a.axisY.type.call(b,b.Axis.units.y,c.normalized.series,j,a.axisY),d.createGridAndLabels(g,i,this.supportsForeignObject,a,this.eventEmitter),f.createGridAndLabels(g,i,this.supportsForeignObject,a,this.eventEmitter),a.showGridBackground&&b.createGridBackground(g,j,a.classNames.gridBackground,this.eventEmitter),c.raw.series.forEach(function(e,g){var i=h.elem("g");i.attr({"ct:series-name":e.name,"ct:meta":b.serialize(e.meta)}),i.addClass([a.classNames.series,e.className||a.classNames.series+"-"+b.alphaNumerate(g)].join(" "));var k=[],l=[];c.normalized.series[g].forEach(function(a,h){var i={x:j.x1+d.projectValue(a,h,c.normalized.series[g]),y:j.y1-f.projectValue(a,h,c.normalized.series[g])};k.push(i.x,i.y),l.push({value:a,valueIndex:h,meta:b.getMetaData(e,h)})}.bind(this));var m={lineSmooth:b.getSeriesOption(e,a,"lineSmooth"),showPoint:b.getSeriesOption(e,a,"showPoint"),showLine:b.getSeriesOption(e,a,"showLine"),showArea:b.getSeriesOption(e,a,"showArea"),areaBase:b.getSeriesOption(e,a,"areaBase")},n="function"==typeof m.lineSmooth?m.lineSmooth:m.lineSmooth?b.Interpolation.monotoneCubic():b.Interpolation.none(),o=n(k,l);if(m.showPoint&&o.pathElements.forEach(function(c){var h=i.elem("line",{x1:c.x,y1:c.y,x2:c.x+.01,y2:c.y},a.classNames.point).attr({"ct:value":[c.data.value.x,c.data.value.y].filter(b.isNumeric).join(","),"ct:meta":b.serialize(c.data.meta)});this.eventEmitter.emit("draw",{type:"point",value:c.data.value,index:c.data.valueIndex,meta:c.data.meta,series:e,seriesIndex:g,axisX:d,axisY:f,group:i,element:h,x:c.x,y:c.y})}.bind(this)),m.showLine){var p=i.elem("path",{d:o.stringify()},a.classNames.line,!0);this.eventEmitter.emit("draw",{type:"line",values:c.normalized.series[g],path:o.clone(),chartRect:j,index:g,series:e,seriesIndex:g,seriesMeta:e.meta,axisX:d,axisY:f,group:i,element:p})}if(m.showArea&&f.range){var q=Math.max(Math.min(m.areaBase,f.range.max),f.range.min),r=j.y1-f.projectValue(q);o.splitByCommand("M").filter(function(a){return a.pathElements.length>1}).map(function(a){var b=a.pathElements[0],c=a.pathElements[a.pathElements.length-1];return a.clone(!0).position(0).remove(1).move(b.x,r).line(b.x,b.y).position(a.pathElements.length+1).line(c.x,r)}).forEach(function(b){var h=i.elem("path",{d:b.stringify()},a.classNames.area,!0);this.eventEmitter.emit("draw",{type:"area",values:c.normalized.series[g],path:b.clone(),series:e,seriesIndex:g,axisX:d,axisY:f,chartRect:j,index:g,group:i,element:h})}.bind(this))}}.bind(this)),this.eventEmitter.emit("created",{bounds:f.bounds,chartRect:j,axisX:d,axisY:f,svg:this.svg,options:a})}function d(a,c,d,f){b.Line["super"].constructor.call(this,a,c,e,b.extend({},e,d),f)}var e=(a.window,a.document,{axisX:{offset:30,position:"end",labelOffset:{x:0,y:0},showLabel:!0,showGrid:!0,labelInterpolationFnc:b.noop,type:void 0},axisY:{offset:40,position:"start",labelOffset:{x:0,y:0},showLabel:!0,showGrid:!0,labelInterpolationFnc:b.noop,type:void 0,scaleMinSpace:20,onlyInteger:!1},width:void 0,height:void 0,showLine:!0,showPoint:!0,showArea:!1,areaBase:0,lineSmooth:!0,showGridBackground:!1,low:void 0,high:void 0,chartPadding:{top:15,right:15,bottom:5,left:10},fullWidth:!1,reverseData:!1,classNames:{chart:"ct-chart-line",label:"ct-label",labelGroup:"ct-labels",series:"ct-series",line:"ct-line",point:"ct-point",area:"ct-area",grid:"ct-grid",gridGroup:"ct-grids",gridBackground:"ct-grid-background",vertical:"ct-vertical",horizontal:"ct-horizontal",start:"ct-start",end:"ct-end"}});b.Line=b.Base.extend({constructor:d,createChart:c})}(this||global,a),function(a,b){"use strict";function c(a){var c,d;a.distributeSeries?(c=b.normalizeData(this.data,a.reverseData,a.horizontalBars?"x":"y"),c.normalized.series=c.normalized.series.map(function(a){return[a]})):c=b.normalizeData(this.data,a.reverseData,a.horizontalBars?"x":"y"),this.svg=b.createSvg(this.container,a.width,a.height,a.classNames.chart+(a.horizontalBars?" "+a.classNames.horizontalBars:""));var f=this.svg.elem("g").addClass(a.classNames.gridGroup),g=this.svg.elem("g"),h=this.svg.elem("g").addClass(a.classNames.labelGroup);
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
