flyonspeed/OnSpeed-Gen2/Software/OnSpeedTeensy_AHRS/LogData.ino

void logData()
{
unsigned long timeStamp=millis(); // save timestamp for logging  
char logLine[2048];
int charsAdded=0;
int boomAge=0;
int efisAge=0;
if (sdLogging)
        {          
          charsAdded+=sprintf(logLine, "%lu,%i,%.2f,%i,%.2f,%.2f,%.2f,%.2f,%.2f,%i,%i",timeStamp,Pfwd,PfwdSmoothed,P45,P45Smoothed,Pstatic,Palt,IAS,AOA,flapsPos,dataMark);
          //charsAdded+=sprintf(logLine, "%lu,%i,%.2f,%i,%.2f,%.2f,%.2f,%.2f,%.2f,%i,%i",timeStamp,124,124.56,145,145.00,1013.00,5600.00,110.58,10.25,2,0);
          #ifdef OAT_AVAILABLE
           charsAdded+=sprintf(logLine+charsAdded, ",%.2f,%.2f",OAT,TAS*MPS2KTS);
          #endif
          
          charsAdded+= sprintf(logLine+charsAdded, ",%.2f,%.6f,%.6f,%.6f,%.6f,%.6f,%.6f,%.2f,%.2f",imuTemp,Az,Ay,Ax,Gx,-Gy,Gz,smoothedPitch,smoothedRoll); // saving negative pitcharate to confirm to Vectrornav notation
          if (readBoom)
            { 
            boomAge=millis()-boomTimestamp;            
            charsAdded+=sprintf(logLine+charsAdded, ",%.2f,%.2f,%.2f,%.2f,%.2f,%i",boomStatic,boomDynamic,boomAlpha,boomBeta,boomIAS,boomAge);
            }         
          if (readEfisData)                         
            {
            efisAge=millis()-efisTimestamp;  
              if (efisID==1) // VN-300 type data
                  {
                  #ifdef VNDEBUG
                  Serial.printf("\nvnAngularRateRoll: %.2f,vnAngularRatePitch: %.2f,vnAngularRateYaw: %.2f,vnVelNedNorth: %.2f,vnVelNedEast: %.2f,vnVelNedDown: %.2f,vnAccelFwd: %.2f,vnAccelLat: %.2f,vnAccelVert: %.2f,vnYaw: %.2f,vnPitch: %.2f,vnRoll: %.2f,vnLinAccFwd: %.2f,vnLinAccLat: %.2f,vnLinAccVert: %.2f,vnYawSigma: %.2f,vnRollSigma: %.2f,vnPitchSigma: %.2f,vnGnssVelNedNorth: %.2f,vnGnssVelNedEast: %.2f,vnGnssVelNedDown: %.2f,vnGPSFix: %i,TimeUTC: %s,vnGnssLat: %.6f,vnGnssLon: %.6f\n",vnAngularRateRoll,vnAngularRatePitch,vnAngularRateYaw,vnVelNedNorth,vnVelNedEast,vnVelNedDown,vnAccelFwd,vnAccelLat,vnAccelVert,vnYaw,vnPitch,vnRoll,vnLinAccFwd,vnLinAccLat,vnLinAccVert,vnYawSigma,vnRollSigma,vnPitchSigma,vnGnssVelNedNorth,vnGnssVelNedEast,vnGnssVelNedDown,vnGPSFix,vnTimeUTC.c_str(),vnGnssLat,vnGnssLon);                  
                  #endif
                  charsAdded+=sprintf(logLine+charsAdded,",%.2f,%.2f,%.2f,%.2f,%.2f,%.2f,%.2f,%.2f,%.2f,%.2f,%.2f,%.2f,%.2f,%.2f,%.2f,%.2f,%.2f,%.2f,%.2f,%.2f,%.2f,%.6f,%.6f,%i,%i,%s",vnAngularRateRoll,vnAngularRatePitch,vnAngularRateYaw,vnVelNedNorth,vnVelNedEast,vnVelNedDown,vnAccelFwd,vnAccelLat,vnAccelVert,vnYaw,vnPitch,vnRoll,vnLinAccFwd,vnLinAccLat,vnLinAccVert,vnYawSigma,vnRollSigma,vnPitchSigma,vnGnssVelNedNorth,vnGnssVelNedEast,vnGnssVelNedDown,vnGnssLat,vnGnssLon,vnGPSFix,efisAge,vnTimeUTC.c_str());                  
                  } else                  
                        {
                        charsAdded+=sprintf(logLine+charsAdded, ",%.2f,%.2f,%.2f,%.2f,%.2f,%i,%i,%i,%.2f,%.2f,%.2f,%.2f,%.2f,%i,%i,%i,%i,%s",efisIAS,efisPitch,efisRoll,efisLateralG,efisVerticalG,efisPercentLift,efisPalt,efisVSI,efisTAS,efisOAT,efisFuelRemaining,efisFuelFlow,efisMAP,efisRPM,efisPercentPower,efisHeading,efisAge,efisTime.c_str());
                        }                        
            }               
          charsAdded+=sprintf(logLine+charsAdded, ",%.2f,%.2f,%.2f,%.2f",earthVertG,flightPath,kalmanVSI*MPS2FPM,kalmanAlt*M2FT);
          sprintf(logLine+charsAdded,"\n");
  //      Serial.print("8");        

#ifdef AGEDEBUG
      Serial.printf("%i,%i\n",boomAge,efisAge);
#endif          
          
        datalogRingBufferAdd(logLine);
        }              
}



void createLogFile()
{
 //sdAvailable=Sd.begin(SdioConfig(FIFO_SDIO));
 if (dataSource=="SENSORS" && sdAvailable)
        {
        Serial.println("SD card initialized. Logging Enabled.");       
        sprintf(filenameSensor,"log_1.csv");        
        int fileCount=1;
        while (Sd.exists(filenameSensor))
              {
              fileCount++;  
              snprintf(filenameSensor, sizeof(filenameSensor), "log_%d.csv", fileCount);   
              }
        Serial.print("Sensor log file:"); Serial.println(filenameSensor);
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
