flyonspeed/OnSpeed-Gen2/Software/OnSpeedTeensy_AHRS/DisplaySerial.ino

void writeSerialData()
{
if (serialOutPort!="NONE" && millis()-serialoutLastUpdate>100) // update every 100ms, 10Hz
    {
    char serialOutString[78];  
          // send serial data if enabled
          
              // send G3X formatted data
              
              int percentLift;
              float displayAOA;
              float displayIAS;
              float smoothingAlphaLat=2.0/(serialDisplaySmoothingLat+1);
              float smoothingAlphaVert=2.0/(serialDisplaySmoothingVert+1);
              int displayVerticalG;
#ifdef SPHERICAL_PROBE
  displayIAS=efisIAS;
#else
  displayIAS=IAS;
#endif      
              if (PaltSmoothed==0) PaltSmoothed=kalmanAlt*M2FT; else PaltSmoothed=kalmanAlt*M2FT * smoothingAlphaVert/10+ (1-smoothingAlphaVert/10)*PaltSmoothed; // increased smoothing needed
              VerticalGSmoothed=aVertCorr * smoothingAlphaVert+ (1-smoothingAlphaVert)*VerticalGSmoothed;
              displayVerticalG=ceil(VerticalGSmoothed * 10.0);
              
              LateralGSmoothed=aLatCorr * smoothingAlphaLat+ (1-smoothingAlphaLat)*LateralGSmoothed;
              // don't output precentLift at low speeds.
              if (displayIAS>=muteAudioUnderIAS)
                  {
                  displayAOA=AOA;                
                  // scale percent lift
                  if (AOA<LDmaxAOA) percentLift=map(AOA,0,LDmaxAOA,0,50);
                      else
                          if (AOA>=LDmaxAOA && AOA<=onSpeedAOAfast) percentLift=map(AOA,LDmaxAOA,onSpeedAOAfast,50,55);
                              else
                                  if (AOA>onSpeedAOAfast && AOA<=onSpeedAOAslow) percentLift=map(AOA,onSpeedAOAfast,onSpeedAOAslow,55,66);
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
